atulravi/picuno/RP2040/software/circuitpython/custom-firmware-2-apr/readme.md

Contains latest Circuit Python package built for Picuno. Yet to request Pull Request. Will do so after files are confirmed to work properly.

<i>Last build date:</i><b>02-Apr-2024</b>
