atulravi/picuno/RP2040/v2/visualplace/readme.md

Files for use in visualPlace for easy assembly of latest PicUNO boards which are production ready without component markers. VisualPlace will display the location of components on the PCB with the BOM and POS files which are provided. 

Download Visual Place here: <a href="https://www.compuphase.com/visualplace/visualplace_en.htm">https://www.compuphase.com/visualplace/visualplace_en.htm</a>
