atulravi/picuno/RP2040/v2/visualplace/2.2.3/readme.md

COntains BOM, Placement file and gerbers to use in VisualPlace for easy assembly.
