atulravi/picuno/RP2040/v2/kicad/v2.2/readme.md

V2.2 with resettable fuse, level shifitng on GPIO 0-5 and standardised 0603 parts for easier assembly. Routing improved in various areas.<br>
Unnecessary vias removed. <br>
Possibly last iteration with changes suggested. <br>
Sparkfun QWIIC added. New notations added. SHall be fabricated for testing soon.
