atulravi/picuno/RP2040/v2/kicad/v2.1/readme.md

Kicad Files for 2.1 with level shifters on GPIO 0-5 and reset pin added.
