atulravi/picuno/RP2040/v2/visualplace/2.2.3/gerbers/readme.md

Gerbers for use in VisualPlace of 2.2.3 ALso applies to 3.3- 1.2.3
