atulravi/picuno/RP2040/v2/kicad/v2.2/2.2.3/readme.md

Final version of the Picuno which will be manufactured soon and is being prototyped as of upload date. KiCad files.
