atulravi/picuno/RP2040/v2/kicad/v2.2/v2.2.1/readme.md

Added India Flag under Flash. Our commitment to Made IN India. Also minor changes. <br>
Also removed 2 logic level changers since cruicial RX TX pins for BLE etc were getting blocked. Not considering replacing it for all pins. <br>
Since 3.3V inputs will be level shifted to 5V. Inputs are not allowed on GPIOs 2-6. Others are perfectly fine. <br>
Qwiic added. Logos added.
