atulravi/picuno/RP2040/v2/scheme-gerbers/gerbers/v2.2/readme.md

Gerbers of  V2.2. Differential routing errors fixed. Minor routing changes. Level Shifting ans QWIIC added.
