atulravi/picuno/RP2040/v2/scheme-gerbers/gerbers/v2.2/2.5.0/README.md

V2.5 Gerbers and files for PicUNO. IOREF issue and RESET PIN issue fixed.
