atulravi/picuno/RP2040/v2/scheme-gerbers/gerbers/v2.2/2.2.5/readme.md

Contains the updated Gerbers for the PicUNO with the IOREF issue fixed.
