atulravi/picuno/RP2040/v2/scheme-gerbers/gerbers/v2.2/v2.2.2/readme.md

V2.2.2 of the Picuno with the Level shifting on the top half of the board. This has been done for easier assembly. Possibly final variant.
