atulravi/picuno/RP2040/v2/scheme-gerbers/gerbers/v2.2/v2.2.1/readme.md

Gerbers with India flag and 2 logic level shifters removed since crucial UART pins were blocked. Also interchanged RX an TX pins to original Arduino UNO posistion upon suggestions. India Flag added due to our commitment of Mae In India!
