atulravi/picuno/RP2040/software/micropython/02-APR-24/frozen_content.c

//
// Content for MICROPY_MODULE_FROZEN_STR
//
#include <stdint.h>
#define MP_FROZEN_STR_NAMES \

const uint32_t mp_frozen_str_sizes[] = { 0 };
const char mp_frozen_str_content[] = {
"\0"
};

//
// Content for MICROPY_MODULE_FROZEN_MPY
//
#include "py/mpconfig.h"
#include "py/objint.h"
#include "py/objstr.h"
#include "py/emitglue.h"
#include "py/nativeglue.h"

#if MICROPY_LONGINT_IMPL != 2
#error "incompatible MICROPY_LONGINT_IMPL"
#endif

#if MPZ_DIG_SIZE != 16
#error "incompatible MPZ_DIG_SIZE"
#endif

#if MICROPY_PY_BUILTINS_FLOAT
typedef struct _mp_obj_float_t {
    mp_obj_base_t base;
    mp_float_t value;
} mp_obj_float_t;
#endif

#if MICROPY_PY_BUILTINS_COMPLEX
typedef struct _mp_obj_complex_t {
    mp_obj_base_t base;
    mp_float_t real;
    mp_float_t imag;
} mp_obj_complex_t;
#endif

enum {
    MP_QSTR_0_dot_1_dot_0 = MP_QSTRnumber_of,
    MP_QSTR_CRC_space_error,
    MP_QSTR_DHT11,
    MP_QSTR_DHT22,
    MP_QSTR_DHTBase,
    MP_QSTR_DS18X20,
    MP_QSTR_Event,
    MP_QSTR_H,
    MP_QSTR_IOQueue,
    MP_QSTR_Lock,
    MP_QSTR_Lock_space_not_space_acquired,
    MP_QSTR_Loop,
    MP_QSTR_MATCH_ROM,
    MP_QSTR_NeoPixel,
    MP_QSTR_ORDER,
    MP_QSTR_OneWire,
    MP_QSTR_OneWireError,
    MP_QSTR_PIOASMEmit,
    MP_QSTR_PIOASMError,
    MP_QSTR_PROTOCOL_TLS_CLIENT,
    MP_QSTR_SEARCH_ROM,
    MP_QSTR_SKIP_ROM,
    MP_QSTR_SOCK_STREAM,
    MP_QSTR_SOL_SOCKET,
    MP_QSTR_SO_REUSEADDR,
    MP_QSTR_SSLContext,
    MP_QSTR_Server,
    MP_QSTR_SingletonGenerator,
    MP_QSTR_Stream,
    MP_QSTR_StreamReader,
    MP_QSTR_StreamWriter,
    MP_QSTR_ThreadSafeFlag,
    MP_QSTR_TimeoutError,
    MP_QSTR__Remove,
    MP_QSTR___version__,
    MP_QSTR__attrs,
    MP_QSTR__boot_dot_py,
    MP_QSTR__boot_fat_dot_py,
    MP_QSTR__dequeue,
    MP_QSTR__enqueue,
    MP_QSTR__exc_context,
    MP_QSTR__exc_handler,
    MP_QSTR__io_queue,
    MP_QSTR__ow,
    MP_QSTR__pio_funcs,
    MP_QSTR__promote_to_task,
    MP_QSTR__run,
    MP_QSTR__search_rom,
    MP_QSTR__serve,
    MP_QSTR__stop_task,
    MP_QSTR__stopper,
    MP_QSTR_accept,
    MP_QSTR_aclose,
    MP_QSTR_asm_pio,
    MP_QSTR_asyncio,
    MP_QSTR_asyncio_slash___init___dot_py,
    MP_QSTR_asyncio_slash_core_dot_py,
    MP_QSTR_asyncio_slash_event_dot_py,
    MP_QSTR_asyncio_slash_funcs_dot_py,
    MP_QSTR_asyncio_slash_lock_dot_py,
    MP_QSTR_asyncio_slash_stream_dot_py,
    MP_QSTR_attr,
    MP_QSTR_autopull,
    MP_QSTR_autopush,
    MP_QSTR_aw,
    MP_QSTR_awrite,
    MP_QSTR_awritestr,
    MP_QSTR_backlog,
    MP_QSTR_bdev,
    MP_QSTR_bind,
    MP_QSTR_block,
    MP_QSTR_bpp,
    MP_QSTR_call_exception_handler,
    MP_QSTR_can_squot_t_space_gather,
    MP_QSTR_cb,
    MP_QSTR_checksum_space_error,
    MP_QSTR_cond,
    MP_QSTR_connect,
    MP_QSTR_context,
    MP_QSTR_convert_temp,
    MP_QSTR_core,
    MP_QSTR_coro_equals_,
    MP_QSTR_coroutine_space_expected,
    MP_QSTR_create_task,
    MP_QSTR_current_task,
    MP_QSTR_dec,
    MP_QSTR_default_exception_handler,
    MP_QSTR_delay,
    MP_QSTR_delay_space_too_space_large,
    MP_QSTR_delay_max,
    MP_QSTR_dest,
    MP_QSTR_dht_dot_py,
    MP_QSTR_diff,
    MP_QSTR_do_handshake_on_connect,
    MP_QSTR_drain,
    MP_QSTR_ds18x20_dot_py,
    MP_QSTR_dt,
    MP_QSTR_duplicate_space_label_space__brace_open__brace_close_,
    MP_QSTR_er,
    MP_QSTR_esp,
    MP_QSTR_event,
    MP_QSTR_exc,
    MP_QSTR_exc_type,
    MP_QSTR_exception,
    MP_QSTR_f,
    MP_QSTR_fifo_join,
    MP_QSTR_fs,
    MP_QSTR_funcs,
    MP_QSTR_future,
    MP_QSTR_future_colon_,
    MP_QSTR_gather,
    MP_QSTR_get_event_loop,
    MP_QSTR_get_exception_handler,
    MP_QSTR_get_extra_info,
    MP_QSTR_getaddrinfo,
    MP_QSTR_gpio,
    MP_QSTR_host,
    MP_QSTR_humidity,
    MP_QSTR_i,
    MP_QSTR_idx,
    MP_QSTR_ifempty,
    MP_QSTR_iffull,
    MP_QSTR_in_,
    MP_QSTR_instr,
    MP_QSTR_invalid_space_bit_space_count_space__brace_open__brace_close_,
    MP_QSTR_is_set,
    MP_QSTR_isr,
    MP_QSTR_jmp,
    MP_QSTR_l_rom,
    MP_QSTR_labels,
    MP_QSTR_listen,
    MP_QSTR_loop,
    MP_QSTR_main_task,
    MP_QSTR_measure,
    MP_QSTR_message,
    MP_QSTR_mod,
    MP_QSTR_n,
    MP_QSTR_neopixel_dot_py,
    MP_QSTR_new_event_loop,
    MP_QSTR_no_space_running_space_event_space_loop,
    MP_QSTR_no_space_sideset,
    MP_QSTR_noblock,
    MP_QSTR_not_osre,
    MP_QSTR_not_x,
    MP_QSTR_not_y,
    MP_QSTR_null,
    MP_QSTR_num_instr,
    MP_QSTR_num_sideset,
    MP_QSTR_onewire_dot_py,
    MP_QSTR_open_connection,
    MP_QSTR_osr,
    MP_QSTR_out,
    MP_QSTR_out_buf,
    MP_QSTR_out_init,
    MP_QSTR_ow,
    MP_QSTR_pass_,
    MP_QSTR_pc,
    MP_QSTR_peername,
    MP_QSTR_pin,
    MP_QSTR_pindirs,
    MP_QSTR_pins,
    MP_QSTR_poller,
    MP_QSTR_port,
    MP_QSTR_pyb,
    MP_QSTR_pyboard,
    MP_QSTR_queue_read,
    MP_QSTR_queue_write,
    MP_QSTR_read_scratch,
    MP_QSTR_read_temp,
    MP_QSTR_readexactly,
    MP_QSTR_rel,
    MP_QSTR_req,
    MP_QSTR_required,
    MP_QSTR_return_exceptions,
    MP_QSTR_rom,
    MP_QSTR_rp2_dot_py,
    MP_QSTR_run,
    MP_QSTR_run_forever,
    MP_QSTR_run_until_complete,
    MP_QSTR_runq_len,
    MP_QSTR_s,
    MP_QSTR_select_rom,
    MP_QSTR_server_hostname,
    MP_QSTR_server_side,
    MP_QSTR_set_exception_handler,
    MP_QSTR_set_init,
    MP_QSTR_setblocking,
    MP_QSTR_setsockopt,
    MP_QSTR_sgen,
    MP_QSTR_side,
    MP_QSTR_sideset_space_too_space_large,
    MP_QSTR_sideset_count,
    MP_QSTR_sideset_init,
    MP_QSTR_sideset_opt,
    MP_QSTR_socket,
    MP_QSTR_src,
    MP_QSTR_ssl,
    MP_QSTR_start_pass,
    MP_QSTR_start_server,
    MP_QSTR_status,
    MP_QSTR_stream,
    MP_QSTR_stream_awrite,
    MP_QSTR_sz,
    MP_QSTR_t,
    MP_QSTR_task,
    MP_QSTR_tb,
    MP_QSTR_temperature,
    MP_QSTR_ticks,
    MP_QSTR_timing,
    MP_QSTR_uasyncio_dot_py,
    MP_QSTR_unknown_space_label_space__brace_open__brace_close_,
    MP_QSTR_v,
    MP_QSTR_value2,
    MP_QSTR_wait,
    MP_QSTR_wait_closed,
    MP_QSTR_wait_for,
    MP_QSTR_wait_for_ms,
    MP_QSTR_wait_io_event,
    MP_QSTR_waiter,
    MP_QSTR_waiting,
    MP_QSTR_waitq_len,
    MP_QSTR_word,
    MP_QSTR_wrap,
    MP_QSTR_wrap_socket,
    MP_QSTR_wrap_target,
    MP_QSTR_wrap_used,
    MP_QSTR_write_scratch,
    MP_QSTR_x,
    MP_QSTR_x_dec,
    MP_QSTR_x_not_y,
    MP_QSTR_y,
    MP_QSTR_y_dec,
};

const qstr_hash_t mp_qstr_frozen_const_hashes[] = {
    20,
    79,
    93,
    253,
    40,
    1,
    233,
    237,
    146,
    142,
    167,
    25,
    185,
    105,
    75,
    104,
    80,
    121,
    244,
    225,
    164,
    203,
    50,
    15,
    33,
    214,
    160,
    57,
    57,
    156,
    54,
    86,
    102,
    124,
    63,
    26,
    171,
    71,
    106,
    192,
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
};

const qstr_len_t mp_qstr_frozen_const_lengths[] = {
    5,
    9,
    5,
    5,
    7,
    7,
    5,
    1,
    7,
    4,
    17,
    4,
    9,
    8,
    5,
    7,
    12,
    10,
    11,
    19,
    10,
    8,
    11,
    10,
    12,
    10,
    6,
    18,
    6,
    12,
    12,
    14,
    12,
    7,
    11,
    6,
    8,
    12,
    8,
    8,
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
};

extern const qstr_pool_t mp_qstr_const_pool;
const qstr_pool_t mp_qstr_frozen_const_pool = {
    &mp_qstr_const_pool, // previous pool
    MP_QSTRnumber_of, // previous pool size
    true, // is_sorted
    10, // allocated entries
    232, // used entries
    (qstr_hash_t *)mp_qstr_frozen_const_hashes,
    (qstr_len_t *)mp_qstr_frozen_const_lengths,
    {
        "0.1.0",
        "CRC error",
        "DHT11",
        "DHT22",
        "DHTBase",
        "DS18X20",
        "Event",
        "H",
        "IOQueue",
        "Lock",
        "Lock not acquired",
        "Loop",
        "MATCH_ROM",
        "NeoPixel",
        "ORDER",
        "OneWire",
        "OneWireError",
        "PIOASMEmit",
        "PIOASMError",
        "PROTOCOL_TLS_CLIENT",
        "SEARCH_ROM",
        "SKIP_ROM",
        "SOCK_STREAM",
        "SOL_SOCKET",
        "SO_REUSEADDR",
        "SSLContext",
        "Server",
        "SingletonGenerator",
        "Stream",
        "StreamReader",
        "StreamWriter",
        "ThreadSafeFlag",
        "TimeoutError",
        "_Remove",
        "__version__",
        "_attrs",
        "_boot.py",
        "_boot_fat.py",
        "_dequeue",
        "_enqueue",
        "_exc_context",
        "_exc_handler",
        "_io_queue",
        "_ow",
        "_pio_funcs",
        "_promote_to_task",
        "_run",
        "_search_rom",
        "_serve",
        "_stop_task",
        "_stopper",
        "accept",
        "aclose",
        "asm_pio",
        "asyncio",
        "asyncio/__init__.py",
        "asyncio/core.py",
        "asyncio/event.py",
        "asyncio/funcs.py",
        "asyncio/lock.py",
        "asyncio/stream.py",
        "attr",
        "autopull",
        "autopush",
        "aw",
        "awrite",
        "awritestr",
        "backlog",
        "bdev",
        "bind",
        "block",
        "bpp",
        "call_exception_handler",
        "can't gather",
        "cb",
        "checksum error",
        "cond",
        "connect",
        "context",
        "convert_temp",
        "core",
        "coro=",
        "coroutine expected",
        "create_task",
        "current_task",
        "dec",
        "default_exception_handler",
        "delay",
        "delay too large",
        "delay_max",
        "dest",
        "dht.py",
        "diff",
        "do_handshake_on_connect",
        "drain",
        "ds18x20.py",
        "dt",
        "duplicate label {}",
        "er",
        "esp",
        "event",
        "exc",
        "exc_type",
        "exception",
        "f",
        "fifo_join",
        "fs",
        "funcs",
        "future",
        "future:",
        "gather",
        "get_event_loop",
        "get_exception_handler",
        "get_extra_info",
        "getaddrinfo",
        "gpio",
        "host",
        "humidity",
        "i",
        "idx",
        "ifempty",
        "iffull",
        "in_",
        "instr",
        "invalid bit count {}",
        "is_set",
        "isr",
        "jmp",
        "l_rom",
        "labels",
        "listen",
        "loop",
        "main_task",
        "measure",
        "message",
        "mod",
        "n",
        "neopixel.py",
        "new_event_loop",
        "no running event loop",
        "no sideset",
        "noblock",
        "not_osre",
        "not_x",
        "not_y",
        "null",
        "num_instr",
        "num_sideset",
        "onewire.py",
        "open_connection",
        "osr",
        "out",
        "out_buf",
        "out_init",
        "ow",
        "pass_",
        "pc",
        "peername",
        "pin",
        "pindirs",
        "pins",
        "poller",
        "port",
        "pyb",
        "pyboard",
        "queue_read",
        "queue_write",
        "read_scratch",
        "read_temp",
        "readexactly",
        "rel",
        "req",
        "required",
        "return_exceptions",
        "rom",
        "rp2.py",
        "run",
        "run_forever",
        "run_until_complete",
        "runq_len",
        "s",
        "select_rom",
        "server_hostname",
        "server_side",
        "set_exception_handler",
        "set_init",
        "setblocking",
        "setsockopt",
        "sgen",
        "side",
        "sideset too large",
        "sideset_count",
        "sideset_init",
        "sideset_opt",
        "socket",
        "src",
        "ssl",
        "start_pass",
        "start_server",
        "status",
        "stream",
        "stream_awrite",
        "sz",
        "t",
        "task",
        "tb",
        "temperature",
        "ticks",
        "timing",
        "uasyncio.py",
        "unknown label {}",
        "v",
        "value2",
        "wait",
        "wait_closed",
        "wait_for",
        "wait_for_ms",
        "wait_io_event",
        "waiter",
        "waiting",
        "waitq_len",
        "word",
        "wrap",
        "wrap_socket",
        "wrap_target",
        "wrap_used",
        "write_scratch",
        "x",
        "x_dec",
        "x_not_y",
        "y",
        "y_dec",
    },
};

////////////////////////////////////////////////////////////////////////////////
// frozen module _boot_fat
// - original source file: /home/atul/micropython/ports/rp2/build-ATRIVATECH_PICUNO/frozen_mpy/_boot_fat.mpy
// - frozen file name: _boot_fat.py
// - .mpy header: 4d:06:00:1f

// frozen bytecode for file _boot_fat.py, scope _boot_fat__lt_module_gt_
static const byte fun_data__boot_fat__lt_module_gt_[96] = {
    0x2c,0x14, // prelude
    0x01, // names: <module>
    0x26,0x6c,0x20,0x28,0x22,0x4d,0x2b,0x2d,0x4b, // code info
    0x80, // LOAD_CONST_SMALL_INT 0
    0x51, // LOAD_CONST_NONE
    0x1b,0x02, // IMPORT_NAME 'vfs'
    0x16,0x02, // STORE_NAME 'vfs'
    0x80, // LOAD_CONST_SMALL_INT 0
    0x51, // LOAD_CONST_NONE
    0x1b,0x03, // IMPORT_NAME 'machine'
    0x16,0x03, // STORE_NAME 'machine'
    0x80, // LOAD_CONST_SMALL_INT 0
    0x51, // LOAD_CONST_NONE
    0x1b,0x04, // IMPORT_NAME 'rp2'
    0x16,0x04, // STORE_NAME 'rp2'
    0x11,0x04, // LOAD_NAME 'rp2'
    0x14,0x05, // LOAD_METHOD 'Flash'
    0x36,0x00, // CALL_METHOD 0
    0x16,0x0a, // STORE_NAME 'bdev'
    0x48,0x0c, // SETUP_EXCEPT 12
    0x11,0x02, // LOAD_NAME 'vfs'
    0x14,0x06, // LOAD_METHOD 'VfsFat'
    0x11,0x0a, // LOAD_NAME 'bdev'
    0x36,0x01, // CALL_METHOD 1
    0x16,0x0b, // STORE_NAME 'fs'
    0x4a,0x19, // POP_EXCEPT_JUMP 25
    0x59, // POP_TOP
    0x11,0x02, // LOAD_NAME 'vfs'
    0x13,0x06, // LOAD_ATTR 'VfsFat'
    0x14,0x07, // LOAD_METHOD 'mkfs'
    0x11,0x0a, // LOAD_NAME 'bdev'
    0x36,0x01, // CALL_METHOD 1
    0x59, // POP_TOP
    0x11,0x02, // LOAD_NAME 'vfs'
    0x14,0x06, // LOAD_METHOD 'VfsFat'
    0x11,0x0a, // LOAD_NAME 'bdev'
    0x36,0x01, // CALL_METHOD 1
    0x16,0x0b, // STORE_NAME 'fs'
    0x4a,0x01, // POP_EXCEPT_JUMP 1
    0x5d, // END_FINALLY
    0x11,0x02, // LOAD_NAME 'vfs'
    0x14,0x08, // LOAD_METHOD 'mount'
    0x11,0x0b, // LOAD_NAME 'fs'
    0x10,0x09, // LOAD_CONST_STRING '/'
    0x36,0x02, // CALL_METHOD 2
    0x59, // POP_TOP
    0x19,0x02, // DELETE_NAME 'vfs'
    0x19,0x0a, // DELETE_NAME 'bdev'
    0x19,0x0b, // DELETE_NAME 'fs'
    0x51, // LOAD_CONST_NONE
    0x63, // RETURN_VALUE
};
#if MICROPY_PERSISTENT_CODE_SAVE
static const mp_raw_code_truncated_t proto_fun__boot_fat__lt_module_gt_ = {
    .proto_fun_indicator[0] = MP_PROTO_FUN_INDICATOR_RAW_CODE_0,
    .proto_fun_indicator[1] = MP_PROTO_FUN_INDICATOR_RAW_CODE_1,
    .kind = MP_CODE_BYTECODE,
    .is_generator = 0,
    .fun_data = fun_data__boot_fat__lt_module_gt_,
    .children = NULL,
    #if MICROPY_PERSISTENT_CODE_SAVE
    .fun_data_len = 96,
    .n_children = 0,
    #if MICROPY_EMIT_MACHINE_CODE
    .prelude_offset = 0,
    #endif
    #if MICROPY_PY_SYS_SETTRACE
    .line_of_definition = 0,
    .prelude = {
        .n_state = 6,
        .n_exc_stack = 1,
        .scope_flags = 0,
        .n_pos_args = 0,
        .n_kwonly_args = 0,
        .n_def_pos_args = 0,
        .qstr_block_name_idx = 1,
        .line_info = fun_data__boot_fat__lt_module_gt_ + 3,
        .line_info_top = fun_data__boot_fat__lt_module_gt_ + 12,
        .opcodes = fun_data__boot_fat__lt_module_gt_ + 12,
    },
    #endif
    #endif
};
#else
#define proto_fun__boot_fat__lt_module_gt_ fun_data__boot_fat__lt_module_gt_[0]
#endif

static const qstr_short_t const_qstr_table_data__boot_fat[12] = {
    MP_QSTR__boot_fat_dot_py,
    MP_QSTR__lt_module_gt_,
    MP_QSTR_vfs,
    MP_QSTR_machine,
    MP_QSTR_rp2,
    MP_QSTR_Flash,
    MP_QSTR_VfsFat,
    MP_QSTR_mkfs,
    MP_QSTR_mount,
    MP_QSTR__slash_,
    MP_QSTR_bdev,
    MP_QSTR_fs,
};

static const mp_frozen_module_t frozen_module__boot_fat = {
    .constants = {
        .qstr_table = (qstr_short_t *)&const_qstr_table_data__boot_fat,
        .obj_table = NULL,
    },
    .proto_fun = &proto_fun__boot_fat__lt_module_gt_,
};

////////////////////////////////////////////////////////////////////////////////
// frozen module _boot
// - original source file: /home/atul/micropython/ports/rp2/build-ATRIVATECH_PICUNO/frozen_mpy/_boot.mpy
// - frozen file name: _boot.py
// - .mpy header: 4d:06:00:1f

// frozen bytecode for file _boot.py, scope _boot__lt_module_gt_
static const byte fun_data__boot__lt_module_gt_[114] = {
    0x3c,0x14, // prelude
    0x01, // names: <module>
    0x26,0x6c,0x40,0x28,0x22,0x53,0x31,0x33,0x4b, // code info
    0x80, // LOAD_CONST_SMALL_INT 0
    0x51, // LOAD_CONST_NONE
    0x1b,0x02, // IMPORT_NAME 'vfs'
    0x16,0x02, // STORE_NAME 'vfs'
    0x80, // LOAD_CONST_SMALL_INT 0
    0x51, // LOAD_CONST_NONE
    0x1b,0x03, // IMPORT_NAME 'machine'
    0x16,0x03, // STORE_NAME 'machine'
    0x80, // LOAD_CONST_SMALL_INT 0
    0x51, // LOAD_CONST_NONE
    0x1b,0x04, // IMPORT_NAME 'rp2'
    0x16,0x04, // STORE_NAME 'rp2'
    0x11,0x04, // LOAD_NAME 'rp2'
    0x14,0x05, // LOAD_METHOD 'Flash'
    0x36,0x00, // CALL_METHOD 0
    0x16,0x0b, // STORE_NAME 'bdev'
    0x48,0x12, // SETUP_EXCEPT 18
    0x11,0x02, // LOAD_NAME 'vfs'
    0x14,0x06, // LOAD_METHOD 'VfsLfs2'
    0x11,0x0b, // LOAD_NAME 'bdev'
    0x10,0x07, // LOAD_CONST_STRING 'progsize'
    0x22,0x82,0x00, // LOAD_CONST_SMALL_INT 256
    0x36,0x82,0x01, // CALL_METHOD 257
    0x16,0x0c, // STORE_NAME 'fs'
    0x4a,0x25, // POP_EXCEPT_JUMP 37
    0x59, // POP_TOP
    0x11,0x02, // LOAD_NAME 'vfs'
    0x13,0x06, // LOAD_ATTR 'VfsLfs2'
    0x14,0x08, // LOAD_METHOD 'mkfs'
    0x11,0x0b, // LOAD_NAME 'bdev'
    0x10,0x07, // LOAD_CONST_STRING 'progsize'
    0x22,0x82,0x00, // LOAD_CONST_SMALL_INT 256
    0x36,0x82,0x01, // CALL_METHOD 257
    0x59, // POP_TOP
    0x11,0x02, // LOAD_NAME 'vfs'
    0x14,0x06, // LOAD_METHOD 'VfsLfs2'
    0x11,0x0b, // LOAD_NAME 'bdev'
    0x10,0x07, // LOAD_CONST_STRING 'progsize'
    0x22,0x82,0x00, // LOAD_CONST_SMALL_INT 256
    0x36,0x82,0x01, // CALL_METHOD 257
    0x16,0x0c, // STORE_NAME 'fs'
    0x4a,0x01, // POP_EXCEPT_JUMP 1
    0x5d, // END_FINALLY
    0x11,0x02, // LOAD_NAME 'vfs'
    0x14,0x09, // LOAD_METHOD 'mount'
    0x11,0x0c, // LOAD_NAME 'fs'
    0x10,0x0a, // LOAD_CONST_STRING '/'
    0x36,0x02, // CALL_METHOD 2
    0x59, // POP_TOP
    0x19,0x02, // DELETE_NAME 'vfs'
    0x19,0x0b, // DELETE_NAME 'bdev'
    0x19,0x0c, // DELETE_NAME 'fs'
    0x51, // LOAD_CONST_NONE
    0x63, // RETURN_VALUE
};
#if MICROPY_PERSISTENT_CODE_SAVE
static const mp_raw_code_truncated_t proto_fun__boot__lt_module_gt_ = {
    .proto_fun_indicator[0] = MP_PROTO_FUN_INDICATOR_RAW_CODE_0,
    .proto_fun_indicator[1] = MP_PROTO_FUN_INDICATOR_RAW_CODE_1,
    .kind = MP_CODE_BYTECODE,
    .is_generator = 0,
    .fun_data = fun_data__boot__lt_module_gt_,
    .children = NULL,
    #if MICROPY_PERSISTENT_CODE_SAVE
    .fun_data_len = 114,
    .n_children = 0,
    #if MICROPY_EMIT_MACHINE_CODE
    .prelude_offset = 0,
    #endif
    #if MICROPY_PY_SYS_SETTRACE
    .line_of_definition = 0,
    .prelude = {
        .n_state = 8,
        .n_exc_stack = 1,
        .scope_flags = 0,
        .n_pos_args = 0,
        .n_kwonly_args = 0,
        .n_def_pos_args = 0,
        .qstr_block_name_idx = 1,
        .line_info = fun_data__boot__lt_module_gt_ + 3,
        .line_info_top = fun_data__boot__lt_module_gt_ + 12,
        .opcodes = fun_data__boot__lt_module_gt_ + 12,
    },
    #endif
    #endif
};
#else
#define proto_fun__boot__lt_module_gt_ fun_data__boot__lt_module_gt_[0]
#endif

static const qstr_short_t const_qstr_table_data__boot[13] = {
    MP_QSTR__boot_dot_py,
    MP_QSTR__lt_module_gt_,
    MP_QSTR_vfs,
    MP_QSTR_machine,
    MP_QSTR_rp2,
    MP_QSTR_Flash,
    MP_QSTR_VfsLfs2,
    MP_QSTR_progsize,
    MP_QSTR_mkfs,
    MP_QSTR_mount,
    MP_QSTR__slash_,
    MP_QSTR_bdev,
    MP_QSTR_fs,
};

static const mp_frozen_module_t frozen_module__boot = {
    .constants = {
        .qstr_table = (qstr_short_t *)&const_qstr_table_data__boot,
        .obj_table = NULL,
    },
    .proto_fun = &proto_fun__boot__lt_module_gt_,
};

////////////////////////////////////////////////////////////////////////////////
// frozen module rp2
// - original source file: /home/atul/micropython/ports/rp2/build-ATRIVATECH_PICUNO/frozen_mpy/rp2.mpy
// - frozen file name: rp2.py
// - .mpy header: 4d:06:00:1f

// frozen bytecode for file rp2.py, scope rp2__lt_module_gt_
static const byte fun_data_rp2__lt_module_gt_[284] = {
    0x18,0x6e, // prelude
    0x01, // names: <module>
    0x60,0x28,0x8c,0x0d,0x6b,0x20,0x89,0x9e,0x42,0x64,0x20,0x24,0x24,0x24,0x24,0x24,0x24,0x24,0x24,0x24,0x44,0x25,0x45,0x24,0x24,0x24,0x24,0x24,0x24,0x44,0x24,0x24,0x26,0x66,0x20,0x26,0x45,0x24,0x24,0x24,0x24,0x24,0x24,0x24,0x24,0x24,0x24,0x24,0x24,0x24,0x66,0x20,0x84,0x29, // code info
    0x80, // LOAD_CONST_SMALL_INT 0
    0x10,0x02, // LOAD_CONST_STRING '*'
    0x2a,0x01, // BUILD_TUPLE 1
    0x1b,0x03, // IMPORT_NAME '_rp2'
    0x69, // IMPORT_STAR
    0x80, // LOAD_CONST_SMALL_INT 0
    0x10,0x04, // LOAD_CONST_STRING 'const'
    0x2a,0x01, // BUILD_TUPLE 1
    0x1b,0x05, // IMPORT_NAME 'micropython'
    0x1c,0x04, // IMPORT_FROM 'const'
    0x16,0x04, // STORE_NAME 'const'
    0x59, // POP_TOP
    0x54, // LOAD_BUILD_CLASS
    0x32,0x00, // MAKE_FUNCTION 0
    0x10,0x06, // LOAD_CONST_STRING 'PIOASMError'
    0x11,0x55, // LOAD_NAME 'Exception'
    0x34,0x03, // CALL_FUNCTION 3
    0x16,0x06, // STORE_NAME 'PIOASMError'
    0x54, // LOAD_BUILD_CLASS
    0x32,0x01, // MAKE_FUNCTION 1
    0x10,0x07, // LOAD_CONST_STRING 'PIOASMEmit'
    0x34,0x02, // CALL_FUNCTION 2
    0x16,0x07, // STORE_NAME 'PIOASMEmit'
    0x2c,0x28, // BUILD_MAP 40
    0x80, // LOAD_CONST_SMALL_INT 0
    0x10,0x08, // LOAD_CONST_STRING 'gpio'
    0x62, // STORE_MAP
    0x80, // LOAD_CONST_SMALL_INT 0
    0x10,0x09, // LOAD_CONST_STRING 'pins'
    0x62, // STORE_MAP
    0x81, // LOAD_CONST_SMALL_INT 1
    0x10,0x0a, // LOAD_CONST_STRING 'x'
    0x62, // STORE_MAP
    0x82, // LOAD_CONST_SMALL_INT 2
    0x10,0x0b, // LOAD_CONST_STRING 'y'
    0x62, // STORE_MAP
    0x83, // LOAD_CONST_SMALL_INT 3
    0x10,0x0c, // LOAD_CONST_STRING 'null'
    0x62, // STORE_MAP
    0x84, // LOAD_CONST_SMALL_INT 4
    0x10,0x0d, // LOAD_CONST_STRING 'pindirs'
    0x62, // STORE_MAP
    0x85, // LOAD_CONST_SMALL_INT 5
    0x10,0x0e, // LOAD_CONST_STRING 'pc'
    0x62, // STORE_MAP
    0x85, // LOAD_CONST_SMALL_INT 5
    0x10,0x0f, // LOAD_CONST_STRING 'status'
    0x62, // STORE_MAP
    0x86, // LOAD_CONST_SMALL_INT 6
    0x10,0x10, // LOAD_CONST_STRING 'isr'
    0x62, // STORE_MAP
    0x87, // LOAD_CONST_SMALL_INT 7
    0x10,0x11, // LOAD_CONST_STRING 'osr'
    0x62, // STORE_MAP
    0x88, // LOAD_CONST_SMALL_INT 8
    0x10,0x12, // LOAD_CONST_STRING 'exec'
    0x62, // STORE_MAP
    0x32,0x02, // MAKE_FUNCTION 2
    0x10,0x13, // LOAD_CONST_STRING 'invert'
    0x62, // STORE_MAP
    0x32,0x03, // MAKE_FUNCTION 3
    0x10,0x14, // LOAD_CONST_STRING 'reverse'
    0x62, // STORE_MAP
    0x81, // LOAD_CONST_SMALL_INT 1
    0x10,0x15, // LOAD_CONST_STRING 'not_x'
    0x62, // STORE_MAP
    0x82, // LOAD_CONST_SMALL_INT 2
    0x10,0x16, // LOAD_CONST_STRING 'x_dec'
    0x62, // STORE_MAP
    0x83, // LOAD_CONST_SMALL_INT 3
    0x10,0x17, // LOAD_CONST_STRING 'not_y'
    0x62, // STORE_MAP
    0x84, // LOAD_CONST_SMALL_INT 4
    0x10,0x18, // LOAD_CONST_STRING 'y_dec'
    0x62, // STORE_MAP
    0x85, // LOAD_CONST_SMALL_INT 5
    0x10,0x19, // LOAD_CONST_STRING 'x_not_y'
    0x62, // STORE_MAP
    0x86, // LOAD_CONST_SMALL_INT 6
    0x10,0x1a, // LOAD_CONST_STRING 'pin'
    0x62, // STORE_MAP
    0x87, // LOAD_CONST_SMALL_INT 7
    0x10,0x1b, // LOAD_CONST_STRING 'not_osre'
    0x62, // STORE_MAP
    0x81, // LOAD_CONST_SMALL_INT 1
    0x10,0x1c, // LOAD_CONST_STRING 'noblock'
    0x62, // STORE_MAP
    0xa1, // LOAD_CONST_SMALL_INT 33
    0x10,0x1d, // LOAD_CONST_STRING 'block'
    0x62, // STORE_MAP
    0x22,0x80,0x40, // LOAD_CONST_SMALL_INT 64
    0x10,0x1e, // LOAD_CONST_STRING 'iffull'
    0x62, // STORE_MAP
    0x22,0x80,0x40, // LOAD_CONST_SMALL_INT 64
    0x10,0x1f, // LOAD_CONST_STRING 'ifempty'
    0x62, // STORE_MAP
    0x22,0x80,0x40, // LOAD_CONST_SMALL_INT 64
    0x10,0x20, // LOAD_CONST_STRING 'clear'
    0x62, // STORE_MAP
    0x32,0x04, // MAKE_FUNCTION 4
    0x10,0x21, // LOAD_CONST_STRING 'rel'
    0x62, // STORE_MAP
    0x51, // LOAD_CONST_NONE
    0x10,0x22, // LOAD_CONST_STRING 'wrap_target'
    0x62, // STORE_MAP
    0x51, // LOAD_CONST_NONE
    0x10,0x23, // LOAD_CONST_STRING 'wrap'
    0x62, // STORE_MAP
    0x51, // LOAD_CONST_NONE
    0x10,0x24, // LOAD_CONST_STRING 'label'
    0x62, // STORE_MAP
    0x51, // LOAD_CONST_NONE
    0x10,0x25, // LOAD_CONST_STRING 'word'
    0x62, // STORE_MAP
    0x51, // LOAD_CONST_NONE
    0x10,0x26, // LOAD_CONST_STRING 'nop'
    0x62, // STORE_MAP
    0x51, // LOAD_CONST_NONE
    0x10,0x27, // LOAD_CONST_STRING 'jmp'
    0x62, // STORE_MAP
    0x51, // LOAD_CONST_NONE
    0x10,0x28, // LOAD_CONST_STRING 'wait'
    0x62, // STORE_MAP
    0x51, // LOAD_CONST_NONE
    0x10,0x29, // LOAD_CONST_STRING 'in_'
    0x62, // STORE_MAP
    0x51, // LOAD_CONST_NONE
    0x10,0x2a, // LOAD_CONST_STRING 'out'
    0x62, // STORE_MAP
    0x51, // LOAD_CONST_NONE
    0x10,0x2b, // LOAD_CONST_STRING 'push'
    0x62, // STORE_MAP
    0x51, // LOAD_CONST_NONE
    0x10,0x2c, // LOAD_CONST_STRING 'pull'
    0x62, // STORE_MAP
    0x51, // LOAD_CONST_NONE
    0x10,0x2d, // LOAD_CONST_STRING 'mov'
    0x62, // STORE_MAP
    0x51, // LOAD_CONST_NONE
    0x10,0x2e, // LOAD_CONST_STRING 'irq'
    0x62, // STORE_MAP
    0x51, // LOAD_CONST_NONE
    0x10,0x2f, // LOAD_CONST_STRING 'set'
    0x62, // STORE_MAP
    0x16,0x56, // STORE_NAME '_pio_funcs'
    0x32,0x05, // MAKE_FUNCTION 5
    0x16,0x3b, // STORE_NAME 'asm_pio'
    0x50, // LOAD_CONST_FALSE
    0x2a,0x01, // BUILD_TUPLE 1
    0x53, // LOAD_NULL
    0x33,0x06, // MAKE_FUNCTION_DEFARGS 6
    0x16,0x3c, // STORE_NAME 'asm_pio_encode'
    0x51, // LOAD_CONST_NONE
    0x63, // RETURN_VALUE
};
// child of rp2__lt_module_gt_
// frozen bytecode for file rp2.py, scope rp2_PIOASMError
static const byte fun_data_rp2_PIOASMError[15] = {
    0x00,0x06, // prelude
    0x06, // names: PIOASMError
    0x88,0x12, // code info
    0x11,0x57, // LOAD_NAME '__name__'
    0x16,0x58, // STORE_NAME '__module__'
    0x10,0x06, // LOAD_CONST_STRING 'PIOASMError'
    0x16,0x59, // STORE_NAME '__qualname__'
    0x51, // LOAD_CONST_NONE
    0x63, // RETURN_VALUE
};
#if MICROPY_PERSISTENT_CODE_SAVE
static const mp_raw_code_truncated_t proto_fun_rp2_PIOASMError = {
    .proto_fun_indicator[0] = MP_PROTO_FUN_INDICATOR_RAW_CODE_0,
    .proto_fun_indicator[1] = MP_PROTO_FUN_INDICATOR_RAW_CODE_1,
    .kind = MP_CODE_BYTECODE,
    .is_generator = 0,
    .fun_data = fun_data_rp2_PIOASMError,
    .children = NULL,
    #if MICROPY_PERSISTENT_CODE_SAVE
    .fun_data_len = 15,
    .n_children = 0,
    #if MICROPY_EMIT_MACHINE_CODE
    .prelude_offset = 0,
    #endif
    #if MICROPY_PY_SYS_SETTRACE
    .line_of_definition = 0,
    .prelude = {
        .n_state = 1,
        .n_exc_stack = 0,
        .scope_flags = 0,
        .n_pos_args = 0,
        .n_kwonly_args = 0,
        .n_def_pos_args = 0,
        .qstr_block_name_idx = 6,
        .line_info = fun_data_rp2_PIOASMError + 3,
        .line_info_top = fun_data_rp2_PIOASMError + 5,
        .opcodes = fun_data_rp2_PIOASMError + 5,
    },
    #endif
    #endif
};
#else
#define proto_fun_rp2_PIOASMError fun_data_rp2_PIOASMError[0]
#endif

// child of rp2__lt_module_gt_
// frozen bytecode for file rp2.py, scope rp2_PIOASMEmit
static const byte fun_data_rp2_PIOASMEmit[191] = {
    0x18,0x4c, // prelude
    0x07, // names: PIOASMEmit
    0x88,0x16,0x1f,0x70,0x80,0x25,0x84,0x0f,0x64,0x84,0x07,0x84,0x0b,0x64,0x64,0x40,0x64,0x60,0x88,0x0c,0x64,0x68,0x60,0x84,0x07,0x64,0x40,0x84,0x07,0x69,0x60,0x69,0x60,0x64,0x40,0x68,0x60, // code info
    0x11,0x57, // LOAD_NAME '__name__'
    0x16,0x58, // STORE_NAME '__module__'
    0x10,0x07, // LOAD_CONST_STRING 'PIOASMEmit'
    0x16,0x59, // STORE_NAME '__qualname__'
    0x53, // LOAD_NULL
    0x2c,0x00, // BUILD_MAP 0
    0x51, // LOAD_CONST_NONE
    0x10,0x30, // LOAD_CONST_STRING 'out_init'
    0x62, // STORE_MAP
    0x51, // LOAD_CONST_NONE
    0x10,0x31, // LOAD_CONST_STRING 'set_init'
    0x62, // STORE_MAP
    0x51, // LOAD_CONST_NONE
    0x10,0x32, // LOAD_CONST_STRING 'sideset_init'
    0x62, // STORE_MAP
    0x80, // LOAD_CONST_SMALL_INT 0
    0x10,0x33, // LOAD_CONST_STRING 'in_shiftdir'
    0x62, // STORE_MAP
    0x80, // LOAD_CONST_SMALL_INT 0
    0x10,0x34, // LOAD_CONST_STRING 'out_shiftdir'
    0x62, // STORE_MAP
    0x50, // LOAD_CONST_FALSE
    0x10,0x35, // LOAD_CONST_STRING 'autopush'
    0x62, // STORE_MAP
    0x50, // LOAD_CONST_FALSE
    0x10,0x36, // LOAD_CONST_STRING 'autopull'
    0x62, // STORE_MAP
    0xa0, // LOAD_CONST_SMALL_INT 32
    0x10,0x37, // LOAD_CONST_STRING 'push_thresh'
    0x62, // STORE_MAP
    0xa0, // LOAD_CONST_SMALL_INT 32
    0x10,0x38, // LOAD_CONST_STRING 'pull_thresh'
    0x62, // STORE_MAP
    0x80, // LOAD_CONST_SMALL_INT 0
    0x10,0x39, // LOAD_CONST_STRING 'fifo_join'
    0x62, // STORE_MAP
    0x33,0x00, // MAKE_FUNCTION_DEFARGS 0
    0x16,0x44, // STORE_NAME '__init__'
    0x32,0x01, // MAKE_FUNCTION 1
    0x16,0x49, // STORE_NAME 'start_pass'
    0x32,0x02, // MAKE_FUNCTION 2
    0x16,0x4a, // STORE_NAME '__getitem__'
    0x32,0x03, // MAKE_FUNCTION 3
    0x16,0x4b, // STORE_NAME 'delay'
    0x32,0x04, // MAKE_FUNCTION 4
    0x16,0x4c, // STORE_NAME 'side'
    0x32,0x05, // MAKE_FUNCTION 5
    0x16,0x22, // STORE_NAME 'wrap_target'
    0x32,0x06, // MAKE_FUNCTION 6
    0x16,0x23, // STORE_NAME 'wrap'
    0x32,0x07, // MAKE_FUNCTION 7
    0x16,0x24, // STORE_NAME 'label'
    0x51, // LOAD_CONST_NONE
    0x2a,0x01, // BUILD_TUPLE 1
    0x53, // LOAD_NULL
    0x33,0x08, // MAKE_FUNCTION_DEFARGS 8
    0x16,0x25, // STORE_NAME 'word'
    0x32,0x09, // MAKE_FUNCTION 9
    0x16,0x26, // STORE_NAME 'nop'
    0x51, // LOAD_CONST_NONE
    0x2a,0x01, // BUILD_TUPLE 1
    0x53, // LOAD_NULL
    0x33,0x0a, // MAKE_FUNCTION_DEFARGS 10
    0x16,0x27, // STORE_NAME 'jmp'
    0x32,0x0b, // MAKE_FUNCTION 11
    0x16,0x28, // STORE_NAME 'wait'
    0x32,0x0c, // MAKE_FUNCTION 12
    0x16,0x29, // STORE_NAME 'in_'
    0x32,0x0d, // MAKE_FUNCTION 13
    0x16,0x2a, // STORE_NAME 'out'
    0x80, // LOAD_CONST_SMALL_INT 0
    0x80, // LOAD_CONST_SMALL_INT 0
    0x2a,0x02, // BUILD_TUPLE 2
    0x53, // LOAD_NULL
    0x33,0x0e, // MAKE_FUNCTION_DEFARGS 14
    0x16,0x2b, // STORE_NAME 'push'
    0x80, // LOAD_CONST_SMALL_INT 0
    0x80, // LOAD_CONST_SMALL_INT 0
    0x2a,0x02, // BUILD_TUPLE 2
    0x53, // LOAD_NULL
    0x33,0x0f, // MAKE_FUNCTION_DEFARGS 15
    0x16,0x2c, // STORE_NAME 'pull'
    0x32,0x10, // MAKE_FUNCTION 16
    0x16,0x2d, // STORE_NAME 'mov'
    0x51, // LOAD_CONST_NONE
    0x2a,0x01, // BUILD_TUPLE 1
    0x53, // LOAD_NULL
    0x33,0x11, // MAKE_FUNCTION_DEFARGS 17
    0x16,0x2e, // STORE_NAME 'irq'
    0x32,0x12, // MAKE_FUNCTION 18
    0x16,0x2f, // STORE_NAME 'set'
    0x51, // LOAD_CONST_NONE
    0x63, // RETURN_VALUE
};
// child of rp2_PIOASMEmit
// frozen bytecode for file rp2.py, scope rp2_PIOASMEmit___init__
static const byte fun_data_rp2_PIOASMEmit___init__[144] = {
    0xa9,0x90,0x88,0x80,0x48,0x3e, // prelude
    0x44,0x5c,0x30,0x31,0x32,0x33,0x34,0x35,0x36,0x37,0x38,0x39, // names: __init__, self, out_init, set_init, sideset_init, in_shiftdir, out_shiftdir, autopush, autopull, push_thresh, pull_thresh, fifo_join
    0x80,0x26,0x4b,0x25,0x22,0x20,0x23,0x26,0x26,0x24,0x24,0x24,0x45,0x51,0x44,0x25,0x26,0x29,0x46, // code info
    0x80, // LOAD_CONST_SMALL_INT 0
    0x10,0x45, // LOAD_CONST_STRING 'array'
    0x2a,0x01, // BUILD_TUPLE 1
    0x1b,0x45, // IMPORT_NAME 'array'
    0x1c,0x45, // IMPORT_FROM 'array'
    0xcb, // STORE_FAST 11
    0x59, // POP_TOP
    0x2c,0x00, // BUILD_MAP 0
    0xb0, // LOAD_FAST 0
    0x18,0x46, // STORE_ATTR 'labels'
    0x80, // LOAD_CONST_SMALL_INT 0
    0xcc, // STORE_FAST 12
    0xba, // LOAD_FAST 10
    0x9e, // LOAD_CONST_SMALL_INT 30
    0xf0, // BINARY_OP 25 __lshift__
    0xb9, // LOAD_FAST 9
    0x9f, // LOAD_CONST_SMALL_INT 31
    0xef, // BINARY_OP 24 __and__
    0x99, // LOAD_CONST_SMALL_INT 25
    0xf0, // BINARY_OP 25 __lshift__
    0xed, // BINARY_OP 22 __or__
    0xb8, // LOAD_FAST 8
    0x9f, // LOAD_CONST_SMALL_INT 31
    0xef, // BINARY_OP 24 __and__
    0x94, // LOAD_CONST_SMALL_INT 20
    0xf0, // BINARY_OP 25 __lshift__
    0xed, // BINARY_OP 22 __or__
    0xb5, // LOAD_FAST 5
    0x93, // LOAD_CONST_SMALL_INT 19
    0xf0, // BINARY_OP 25 __lshift__
    0xed, // BINARY_OP 22 __or__
    0xb4, // LOAD_FAST 4
    0x92, // LOAD_CONST_SMALL_INT 18
    0xf0, // BINARY_OP 25 __lshift__
    0xed, // BINARY_OP 22 __or__
    0xb7, // LOAD_FAST 7
    0x91, // LOAD_CONST_SMALL_INT 17
    0xf0, // BINARY_OP 25 __lshift__
    0xed, // BINARY_OP 22 __or__
    0xb6, // LOAD_FAST 6
    0x90, // LOAD_CONST_SMALL_INT 16
    0xf0, // BINARY_OP 25 __lshift__
    0xed, // BINARY_OP 22 __or__
    0xcd, // STORE_FAST 13
    0xbb, // LOAD_FAST 11
    0x10,0x47, // LOAD_CONST_STRING 'H'
    0x34,0x01, // CALL_FUNCTION 1
    0x7f, // LOAD_CONST_SMALL_INT -1
    0x7f, // LOAD_CONST_SMALL_INT -1
    0xbc, // LOAD_FAST 12
    0xbd, // LOAD_FAST 13
    0xb1, // LOAD_FAST 1
    0xb2, // LOAD_FAST 2
    0xb3, // LOAD_FAST 3
    0x2b,0x08, // BUILD_LIST 8
    0xb0, // LOAD_FAST 0
    0x18,0x43, // STORE_ATTR 'prog'
    0x50, // LOAD_CONST_FALSE
    0xb0, // LOAD_FAST 0
    0x18,0x48, // STORE_ATTR 'wrap_used'
    0xb3, // LOAD_FAST 3
    0x51, // LOAD_CONST_NONE
    0xde, // BINARY_OP 7 <is>
    0x44,0x46, // POP_JUMP_IF_FALSE 6
    0x80, // LOAD_CONST_SMALL_INT 0
    0xb0, // LOAD_FAST 0
    0x18,0x3d, // STORE_ATTR 'sideset_count'
    0x42,0x57, // JUMP 23
    0x12,0x5d, // LOAD_GLOBAL 'isinstance'
    0xb3, // LOAD_FAST 3
    0x12,0x5e, // LOAD_GLOBAL 'int'
    0x34,0x02, // CALL_FUNCTION 2
    0x44,0x46, // POP_JUMP_IF_FALSE 6
    0x81, // LOAD_CONST_SMALL_INT 1
    0xb0, // LOAD_FAST 0
    0x18,0x3d, // STORE_ATTR 'sideset_count'
    0x42,0x48, // JUMP 8
    0x12,0x5b, // LOAD_GLOBAL 'len'
    0xb3, // LOAD_FAST 3
    0x34,0x01, // CALL_FUNCTION 1
    0xb0, // LOAD_FAST 0
    0x18,0x3d, // STORE_ATTR 'sideset_count'
    0x51, // LOAD_CONST_NONE
    0x63, // RETURN_VALUE
};
#if MICROPY_PERSISTENT_CODE_SAVE
static const mp_raw_code_truncated_t proto_fun_rp2_PIOASMEmit___init__ = {
    .proto_fun_indicator[0] = MP_PROTO_FUN_INDICATOR_RAW_CODE_0,
    .proto_fun_indicator[1] = MP_PROTO_FUN_INDICATOR_RAW_CODE_1,
    .kind = MP_CODE_BYTECODE,
    .is_generator = 0,
    .fun_data = fun_data_rp2_PIOASMEmit___init__,
    .children = NULL,
    #if MICROPY_PERSISTENT_CODE_SAVE
    .fun_data_len = 144,
    .n_children = 0,
    #if MICROPY_EMIT_MACHINE_CODE
    .prelude_offset = 0,
    #endif
    #if MICROPY_PY_SYS_SETTRACE
    .line_of_definition = 0,
    .prelude = {
        .n_state = 22,
        .n_exc_stack = 0,
        .scope_flags = 8,
        .n_pos_args = 1,
        .n_kwonly_args = 10,
        .n_def_pos_args = 0,
        .qstr_block_name_idx = 68,
        .line_info = fun_data_rp2_PIOASMEmit___init__ + 18,
        .line_info_top = fun_data_rp2_PIOASMEmit___init__ + 37,
        .opcodes = fun_data_rp2_PIOASMEmit___init__ + 37,
    },
    #endif
    #endif
};
#else
#define proto_fun_rp2_PIOASMEmit___init__ fun_data_rp2_PIOASMEmit___init__[0]
#endif

// child of rp2_PIOASMEmit
// frozen bytecode for file rp2.py, scope rp2_PIOASMEmit_start_pass
static const byte fun_data_rp2_PIOASMEmit_start_pass[110] = {
    0x2a,0x22, // prelude
    0x49,0x5c,0x40, // names: start_pass, self, pass_
    0x80,0x3f,0x26,0x2a,0x26,0x24,0x25,0x2a,0x25,0x2b,0x29,0x2b,0x24,0x24, // code info
    0xb1, // LOAD_FAST 1
    0x81, // LOAD_CONST_SMALL_INT 1
    0xd9, // BINARY_OP 2 __eq__
    0x44,0xc7,0x80, // POP_JUMP_IF_FALSE 71
    0xb0, // LOAD_FAST 0
    0x13,0x48, // LOAD_ATTR 'wrap_used'
    0x43,0x4b, // POP_JUMP_IF_TRUE 11
    0xb0, // LOAD_FAST 0
    0x13,0x41, // LOAD_ATTR 'num_instr'
    0x44,0x46, // POP_JUMP_IF_FALSE 6
    0xb0, // LOAD_FAST 0
    0x14,0x23, // LOAD_METHOD 'wrap'
    0x36,0x00, // CALL_METHOD 0
    0x59, // POP_TOP
    0x9f, // LOAD_CONST_SMALL_INT 31
    0xb0, // LOAD_FAST 0
    0x18,0x3f, // STORE_ATTR 'delay_max'
    0xb0, // LOAD_FAST 0
    0x13,0x3d, // LOAD_ATTR 'sideset_count'
    0x44,0x6e, // POP_JUMP_IF_FALSE 46
    0xb0, // LOAD_FAST 0
    0x13,0x42, // LOAD_ATTR 'num_sideset'
    0xb0, // LOAD_FAST 0
    0x13,0x41, // LOAD_ATTR 'num_instr'
    0xdc, // BINARY_OP 5 __ne__
    0xb0, // LOAD_FAST 0
    0x18,0x3e, // STORE_ATTR 'sideset_opt'
    0xb0, // LOAD_FAST 0
    0x13,0x3e, // LOAD_ATTR 'sideset_opt'
    0x44,0x54, // POP_JUMP_IF_FALSE 20
    0xb0, // LOAD_FAST 0
    0x13,0x43, // LOAD_ATTR 'prog'
    0x83, // LOAD_CONST_SMALL_INT 3
    0x58, // DUP_TOP_TWO
    0x55, // LOAD_SUBSCR
    0x23,0x01, // LOAD_CONST_OBJ 1
    0xe0, // BINARY_OP 9 __ior__
    0x5b, // ROT_THREE
    0x56, // STORE_SUBSCR
    0xb0, // LOAD_FAST 0
    0x57, // DUP_TOP
    0x13,0x3d, // LOAD_ATTR 'sideset_count'
    0x81, // LOAD_CONST_SMALL_INT 1
    0xe5, // BINARY_OP 14 __iadd__
    0x5a, // ROT_TWO
    0x18,0x3d, // STORE_ATTR 'sideset_count'
    0xb0, // LOAD_FAST 0
    0x57, // DUP_TOP
    0x13,0x3f, // LOAD_ATTR 'delay_max'
    0xb0, // LOAD_FAST 0
    0x13,0x3d, // LOAD_ATTR 'sideset_count'
    0xe4, // BINARY_OP 13 __irshift__
    0x5a, // ROT_TWO
    0x18,0x3f, // STORE_ATTR 'delay_max'
    0xb1, // LOAD_FAST 1
    0xb0, // LOAD_FAST 0
    0x18,0x40, // STORE_ATTR 'pass_'
    0x80, // LOAD_CONST_SMALL_INT 0
    0xb0, // LOAD_FAST 0
    0x18,0x41, // STORE_ATTR 'num_instr'
    0x80, // LOAD_CONST_SMALL_INT 0
    0xb0, // LOAD_FAST 0
    0x18,0x42, // STORE_ATTR 'num_sideset'
    0x51, // LOAD_CONST_NONE
    0x63, // RETURN_VALUE
};
#if MICROPY_PERSISTENT_CODE_SAVE
static const mp_raw_code_truncated_t proto_fun_rp2_PIOASMEmit_start_pass = {
    .proto_fun_indicator[0] = MP_PROTO_FUN_INDICATOR_RAW_CODE_0,
    .proto_fun_indicator[1] = MP_PROTO_FUN_INDICATOR_RAW_CODE_1,
    .kind = MP_CODE_BYTECODE,
    .is_generator = 0,
    .fun_data = fun_data_rp2_PIOASMEmit_start_pass,
    .children = NULL,
    #if MICROPY_PERSISTENT_CODE_SAVE
    .fun_data_len = 110,
    .n_children = 0,
    #if MICROPY_EMIT_MACHINE_CODE
    .prelude_offset = 0,
    #endif
    #if MICROPY_PY_SYS_SETTRACE
    .line_of_definition = 0,
    .prelude = {
        .n_state = 6,
        .n_exc_stack = 0,
        .scope_flags = 0,
        .n_pos_args = 2,
        .n_kwonly_args = 0,
        .n_def_pos_args = 0,
        .qstr_block_name_idx = 73,
        .line_info = fun_data_rp2_PIOASMEmit_start_pass + 5,
        .line_info_top = fun_data_rp2_PIOASMEmit_start_pass + 19,
        .opcodes = fun_data_rp2_PIOASMEmit_start_pass + 19,
    },
    #endif
    #endif
};
#else
#define proto_fun_rp2_PIOASMEmit_start_pass fun_data_rp2_PIOASMEmit_start_pass[0]
#endif

// child of rp2_PIOASMEmit
// frozen bytecode for file rp2.py, scope rp2_PIOASMEmit___getitem__
static const byte fun_data_rp2_PIOASMEmit___getitem__[14] = {
    0x22,0x0a, // prelude
    0x4a,0x5c,0x5f, // names: __getitem__, self, key
    0x80,0x4e, // code info
    0xb0, // LOAD_FAST 0
    0x14,0x4b, // LOAD_METHOD 'delay'
    0xb1, // LOAD_FAST 1
    0x36,0x01, // CALL_METHOD 1
    0x63, // RETURN_VALUE
};
#if MICROPY_PERSISTENT_CODE_SAVE
static const mp_raw_code_truncated_t proto_fun_rp2_PIOASMEmit___getitem__ = {
    .proto_fun_indicator[0] = MP_PROTO_FUN_INDICATOR_RAW_CODE_0,
    .proto_fun_indicator[1] = MP_PROTO_FUN_INDICATOR_RAW_CODE_1,
    .kind = MP_CODE_BYTECODE,
    .is_generator = 0,
    .fun_data = fun_data_rp2_PIOASMEmit___getitem__,
    .children = NULL,
    #if MICROPY_PERSISTENT_CODE_SAVE
    .fun_data_len = 14,
    .n_children = 0,
    #if MICROPY_EMIT_MACHINE_CODE
    .prelude_offset = 0,
    #endif
    #if MICROPY_PY_SYS_SETTRACE
    .line_of_definition = 0,
    .prelude = {
        .n_state = 5,
        .n_exc_stack = 0,
        .scope_flags = 0,
        .n_pos_args = 2,
        .n_kwonly_args = 0,
        .n_def_pos_args = 0,
        .qstr_block_name_idx = 74,
        .line_info = fun_data_rp2_PIOASMEmit___getitem__ + 5,
        .line_info_top = fun_data_rp2_PIOASMEmit___getitem__ + 7,
        .opcodes = fun_data_rp2_PIOASMEmit___getitem__ + 7,
    },
    #endif
    #endif
};
#else
#define proto_fun_rp2_PIOASMEmit___getitem__ fun_data_rp2_PIOASMEmit___getitem__[0]
#endif

// child of rp2_PIOASMEmit
// frozen bytecode for file rp2.py, scope rp2_PIOASMEmit_delay
static const byte fun_data_rp2_PIOASMEmit_delay[48] = {
    0x32,0x12, // prelude
    0x4b,0x5c,0x4b, // names: delay, self, delay
    0x80,0x51,0x27,0x27,0x27,0x2e, // code info
    0xb0, // LOAD_FAST 0
    0x13,0x40, // LOAD_ATTR 'pass_'
    0x80, // LOAD_CONST_SMALL_INT 0
    0xd8, // BINARY_OP 1 __gt__
    0x44,0x5c, // POP_JUMP_IF_FALSE 28
    0xb1, // LOAD_FAST 1
    0xb0, // LOAD_FAST 0
    0x13,0x3f, // LOAD_ATTR 'delay_max'
    0xd8, // BINARY_OP 1 __gt__
    0x44,0x47, // POP_JUMP_IF_FALSE 7
    0x12,0x06, // LOAD_GLOBAL 'PIOASMError'
    0x23,0x02, // LOAD_CONST_OBJ 2
    0x34,0x01, // CALL_FUNCTION 1
    0x65, // RAISE_OBJ
    0xb0, // LOAD_FAST 0
    0x13,0x43, // LOAD_ATTR 'prog'
    0x80, // LOAD_CONST_SMALL_INT 0
    0x55, // LOAD_SUBSCR
    0x7f, // LOAD_CONST_SMALL_INT -1
    0x58, // DUP_TOP_TWO
    0x55, // LOAD_SUBSCR
    0xb1, // LOAD_FAST 1
    0x88, // LOAD_CONST_SMALL_INT 8
    0xf0, // BINARY_OP 25 __lshift__
    0xe0, // BINARY_OP 9 __ior__
    0x5b, // ROT_THREE
    0x56, // STORE_SUBSCR
    0xb0, // LOAD_FAST 0
    0x63, // RETURN_VALUE
};
#if MICROPY_PERSISTENT_CODE_SAVE
static const mp_raw_code_truncated_t proto_fun_rp2_PIOASMEmit_delay = {
    .proto_fun_indicator[0] = MP_PROTO_FUN_INDICATOR_RAW_CODE_0,
    .proto_fun_indicator[1] = MP_PROTO_FUN_INDICATOR_RAW_CODE_1,
    .kind = MP_CODE_BYTECODE,
    .is_generator = 0,
    .fun_data = fun_data_rp2_PIOASMEmit_delay,
    .children = NULL,
    #if MICROPY_PERSISTENT_CODE_SAVE
    .fun_data_len = 48,
    .n_children = 0,
    #if MICROPY_EMIT_MACHINE_CODE
    .prelude_offset = 0,
    #endif
    #if MICROPY_PY_SYS_SETTRACE
    .line_of_definition = 0,
    .prelude = {
        .n_state = 7,
        .n_exc_stack = 0,
        .scope_flags = 0,
        .n_pos_args = 2,
        .n_kwonly_args = 0,
        .n_def_pos_args = 0,
        .qstr_block_name_idx = 75,
        .line_info = fun_data_rp2_PIOASMEmit_delay + 5,
        .line_info_top = fun_data_rp2_PIOASMEmit_delay + 11,
        .opcodes = fun_data_rp2_PIOASMEmit_delay + 11,
    },
    #endif
    #endif
};
#else
#define proto_fun_rp2_PIOASMEmit_delay fun_data_rp2_PIOASMEmit_delay[0]
#endif

// child of rp2_PIOASMEmit
// frozen bytecode for file rp2.py, scope rp2_PIOASMEmit_side
static const byte fun_data_rp2_PIOASMEmit_side[89] = {
    0x42,0x1a, // prelude
    0x4c,0x5c,0x60, // names: side, self, value
    0x80,0x58,0x29,0x27,0x27,0x27,0x29,0x27,0x26,0x34, // code info
    0xb0, // LOAD_FAST 0
    0x57, // DUP_TOP
    0x13,0x42, // LOAD_ATTR 'num_sideset'
    0x81, // LOAD_CONST_SMALL_INT 1
    0xe5, // BINARY_OP 14 __iadd__
    0x5a, // ROT_TWO
    0x18,0x42, // STORE_ATTR 'num_sideset'
    0xb0, // LOAD_FAST 0
    0x13,0x40, // LOAD_ATTR 'pass_'
    0x80, // LOAD_CONST_SMALL_INT 0
    0xd8, // BINARY_OP 1 __gt__
    0x44,0x78, // POP_JUMP_IF_FALSE 56
    0xb0, // LOAD_FAST 0
    0x13,0x3d, // LOAD_ATTR 'sideset_count'
    0x80, // LOAD_CONST_SMALL_INT 0
    0xd9, // BINARY_OP 2 __eq__
    0x44,0x47, // POP_JUMP_IF_FALSE 7
    0x12,0x06, // LOAD_GLOBAL 'PIOASMError'
    0x10,0x4d, // LOAD_CONST_STRING 'no sideset'
    0x34,0x01, // CALL_FUNCTION 1
    0x65, // RAISE_OBJ
    0xb1, // LOAD_FAST 1
    0x81, // LOAD_CONST_SMALL_INT 1
    0xb0, // LOAD_FAST 0
    0x13,0x3d, // LOAD_ATTR 'sideset_count'
    0xf0, // BINARY_OP 25 __lshift__
    0xdb, // BINARY_OP 4 __ge__
    0x44,0x47, // POP_JUMP_IF_FALSE 7
    0x12,0x06, // LOAD_GLOBAL 'PIOASMError'
    0x23,0x03, // LOAD_CONST_OBJ 3
    0x34,0x01, // CALL_FUNCTION 1
    0x65, // RAISE_OBJ
    0x8d, // LOAD_CONST_SMALL_INT 13
    0xb0, // LOAD_FAST 0
    0x13,0x3d, // LOAD_ATTR 'sideset_count'
    0xf3, // BINARY_OP 28 __sub__
    0xc2, // STORE_FAST 2
    0xb0, // LOAD_FAST 0
    0x13,0x43, // LOAD_ATTR 'prog'
    0x80, // LOAD_CONST_SMALL_INT 0
    0x55, // LOAD_SUBSCR
    0x7f, // LOAD_CONST_SMALL_INT -1
    0x58, // DUP_TOP_TWO
    0x55, // LOAD_SUBSCR
    0xb0, // LOAD_FAST 0
    0x13,0x3e, // LOAD_ATTR 'sideset_opt'
    0x8c, // LOAD_CONST_SMALL_INT 12
    0xf0, // BINARY_OP 25 __lshift__
    0xb1, // LOAD_FAST 1
    0xb2, // LOAD_FAST 2
    0xf0, // BINARY_OP 25 __lshift__
    0xed, // BINARY_OP 22 __or__
    0xe0, // BINARY_OP 9 __ior__
    0x5b, // ROT_THREE
    0x56, // STORE_SUBSCR
    0xb0, // LOAD_FAST 0
    0x63, // RETURN_VALUE
};
#if MICROPY_PERSISTENT_CODE_SAVE
static const mp_raw_code_truncated_t proto_fun_rp2_PIOASMEmit_side = {
    .proto_fun_indicator[0] = MP_PROTO_FUN_INDICATOR_RAW_CODE_0,
    .proto_fun_indicator[1] = MP_PROTO_FUN_INDICATOR_RAW_CODE_1,
    .kind = MP_CODE_BYTECODE,
    .is_generator = 0,
    .fun_data = fun_data_rp2_PIOASMEmit_side,
    .children = NULL,
    #if MICROPY_PERSISTENT_CODE_SAVE
    .fun_data_len = 89,
    .n_children = 0,
    #if MICROPY_EMIT_MACHINE_CODE
    .prelude_offset = 0,
    #endif
    #if MICROPY_PY_SYS_SETTRACE
    .line_of_definition = 0,
    .prelude = {
        .n_state = 9,
        .n_exc_stack = 0,
        .scope_flags = 0,
        .n_pos_args = 2,
        .n_kwonly_args = 0,
        .n_def_pos_args = 0,
        .qstr_block_name_idx = 76,
        .line_info = fun_data_rp2_PIOASMEmit_side + 5,
        .line_info_top = fun_data_rp2_PIOASMEmit_side + 15,
        .opcodes = fun_data_rp2_PIOASMEmit_side + 15,
    },
    #endif
    #endif
};
#else
#define proto_fun_rp2_PIOASMEmit_side fun_data_rp2_PIOASMEmit_side[0]
#endif

// child of rp2_PIOASMEmit
// frozen bytecode for file rp2.py, scope rp2_PIOASMEmit_wrap_target
static const byte fun_data_rp2_PIOASMEmit_wrap_target[22] = {
    0x29,0x08, // prelude
    0x22,0x5c, // names: wrap_target, self
    0x80,0x63, // code info
    0xb0, // LOAD_FAST 0
    0x13,0x43, // LOAD_ATTR 'prog'
    0x83, // LOAD_CONST_SMALL_INT 3
    0x58, // DUP_TOP_TWO
    0x55, // LOAD_SUBSCR
    0xb0, // LOAD_FAST 0
    0x13,0x41, // LOAD_ATTR 'num_instr'
    0x87, // LOAD_CONST_SMALL_INT 7
    0xf0, // BINARY_OP 25 __lshift__
    0xe0, // BINARY_OP 9 __ior__
    0x5b, // ROT_THREE
    0x56, // STORE_SUBSCR
    0x51, // LOAD_CONST_NONE
    0x63, // RETURN_VALUE
};
#if MICROPY_PERSISTENT_CODE_SAVE
static const mp_raw_code_truncated_t proto_fun_rp2_PIOASMEmit_wrap_target = {
    .proto_fun_indicator[0] = MP_PROTO_FUN_INDICATOR_RAW_CODE_0,
    .proto_fun_indicator[1] = MP_PROTO_FUN_INDICATOR_RAW_CODE_1,
    .kind = MP_CODE_BYTECODE,
    .is_generator = 0,
    .fun_data = fun_data_rp2_PIOASMEmit_wrap_target,
    .children = NULL,
    #if MICROPY_PERSISTENT_CODE_SAVE
    .fun_data_len = 22,
    .n_children = 0,
    #if MICROPY_EMIT_MACHINE_CODE
    .prelude_offset = 0,
    #endif
    #if MICROPY_PY_SYS_SETTRACE
    .line_of_definition = 0,
    .prelude = {
        .n_state = 6,
        .n_exc_stack = 0,
        .scope_flags = 0,
        .n_pos_args = 1,
        .n_kwonly_args = 0,
        .n_def_pos_args = 0,
        .qstr_block_name_idx = 34,
        .line_info = fun_data_rp2_PIOASMEmit_wrap_target + 4,
        .line_info_top = fun_data_rp2_PIOASMEmit_wrap_target + 6,
        .opcodes = fun_data_rp2_PIOASMEmit_wrap_target + 6,
    },
    #endif
    #endif
};
#else
#define proto_fun_rp2_PIOASMEmit_wrap_target fun_data_rp2_PIOASMEmit_wrap_target[0]
#endif

// child of rp2_PIOASMEmit
// frozen bytecode for file rp2.py, scope rp2_PIOASMEmit_wrap
static const byte fun_data_rp2_PIOASMEmit_wrap[38] = {
    0x29,0x0c, // prelude
    0x23,0x5c, // names: wrap, self
    0x80,0x66,0x28,0x30, // code info
    0xb0, // LOAD_FAST 0
    0x13,0x41, // LOAD_ATTR 'num_instr'
    0x43,0x43, // POP_JUMP_IF_TRUE 3
    0x12,0x4e, // LOAD_GLOBAL 'AssertionError'
    0x65, // RAISE_OBJ
    0xb0, // LOAD_FAST 0
    0x13,0x43, // LOAD_ATTR 'prog'
    0x83, // LOAD_CONST_SMALL_INT 3
    0x58, // DUP_TOP_TWO
    0x55, // LOAD_SUBSCR
    0xb0, // LOAD_FAST 0
    0x13,0x41, // LOAD_ATTR 'num_instr'
    0x81, // LOAD_CONST_SMALL_INT 1
    0xf3, // BINARY_OP 28 __sub__
    0x8c, // LOAD_CONST_SMALL_INT 12
    0xf0, // BINARY_OP 25 __lshift__
    0xe0, // BINARY_OP 9 __ior__
    0x5b, // ROT_THREE
    0x56, // STORE_SUBSCR
    0x52, // LOAD_CONST_TRUE
    0xb0, // LOAD_FAST 0
    0x18,0x48, // STORE_ATTR 'wrap_used'
    0x51, // LOAD_CONST_NONE
    0x63, // RETURN_VALUE
};
#if MICROPY_PERSISTENT_CODE_SAVE
static const mp_raw_code_truncated_t proto_fun_rp2_PIOASMEmit_wrap = {
    .proto_fun_indicator[0] = MP_PROTO_FUN_INDICATOR_RAW_CODE_0,
    .proto_fun_indicator[1] = MP_PROTO_FUN_INDICATOR_RAW_CODE_1,
    .kind = MP_CODE_BYTECODE,
    .is_generator = 0,
    .fun_data = fun_data_rp2_PIOASMEmit_wrap,
    .children = NULL,
    #if MICROPY_PERSISTENT_CODE_SAVE
    .fun_data_len = 38,
    .n_children = 0,
    #if MICROPY_EMIT_MACHINE_CODE
    .prelude_offset = 0,
    #endif
    #if MICROPY_PY_SYS_SETTRACE
    .line_of_definition = 0,
    .prelude = {
        .n_state = 6,
        .n_exc_stack = 0,
        .scope_flags = 0,
        .n_pos_args = 1,
        .n_kwonly_args = 0,
        .n_def_pos_args = 0,
        .qstr_block_name_idx = 35,
        .line_info = fun_data_rp2_PIOASMEmit_wrap + 4,
        .line_info_top = fun_data_rp2_PIOASMEmit_wrap + 8,
        .opcodes = fun_data_rp2_PIOASMEmit_wrap + 8,
    },
    #endif
    #endif
};
#else
#define proto_fun_rp2_PIOASMEmit_wrap fun_data_rp2_PIOASMEmit_wrap[0]
#endif

// child of rp2_PIOASMEmit
// frozen bytecode for file rp2.py, scope rp2_PIOASMEmit_label
static const byte fun_data_rp2_PIOASMEmit_label[46] = {
    0x2a,0x10, // prelude
    0x24,0x5c,0x24, // names: label, self, label
    0x80,0x6b,0x27,0x27,0x2c, // code info
    0xb0, // LOAD_FAST 0
    0x13,0x40, // LOAD_ATTR 'pass_'
    0x80, // LOAD_CONST_SMALL_INT 0
    0xd9, // BINARY_OP 2 __eq__
    0x44,0x5b, // POP_JUMP_IF_FALSE 27
    0xb1, // LOAD_FAST 1
    0xb0, // LOAD_FAST 0
    0x13,0x46, // LOAD_ATTR 'labels'
    0xdd, // BINARY_OP 6 <in>
    0x44,0x4c, // POP_JUMP_IF_FALSE 12
    0x12,0x06, // LOAD_GLOBAL 'PIOASMError'
    0x23,0x04, // LOAD_CONST_OBJ 4
    0x14,0x4f, // LOAD_METHOD 'format'
    0xb1, // LOAD_FAST 1
    0x36,0x01, // CALL_METHOD 1
    0x34,0x01, // CALL_FUNCTION 1
    0x65, // RAISE_OBJ
    0xb0, // LOAD_FAST 0
    0x13,0x41, // LOAD_ATTR 'num_instr'
    0xb0, // LOAD_FAST 0
    0x13,0x46, // LOAD_ATTR 'labels'
    0xb1, // LOAD_FAST 1
    0x56, // STORE_SUBSCR
    0x51, // LOAD_CONST_NONE
    0x63, // RETURN_VALUE
};
#if MICROPY_PERSISTENT_CODE_SAVE
static const mp_raw_code_truncated_t proto_fun_rp2_PIOASMEmit_label = {
    .proto_fun_indicator[0] = MP_PROTO_FUN_INDICATOR_RAW_CODE_0,
    .proto_fun_indicator[1] = MP_PROTO_FUN_INDICATOR_RAW_CODE_1,
    .kind = MP_CODE_BYTECODE,
    .is_generator = 0,
    .fun_data = fun_data_rp2_PIOASMEmit_label,
    .children = NULL,
    #if MICROPY_PERSISTENT_CODE_SAVE
    .fun_data_len = 46,
    .n_children = 0,
    #if MICROPY_EMIT_MACHINE_CODE
    .prelude_offset = 0,
    #endif
    #if MICROPY_PY_SYS_SETTRACE
    .line_of_definition = 0,
    .prelude = {
        .n_state = 6,
        .n_exc_stack = 0,
        .scope_flags = 0,
        .n_pos_args = 2,
        .n_kwonly_args = 0,
        .n_def_pos_args = 0,
        .qstr_block_name_idx = 36,
        .line_info = fun_data_rp2_PIOASMEmit_label + 5,
        .line_info_top = fun_data_rp2_PIOASMEmit_label + 10,
        .opcodes = fun_data_rp2_PIOASMEmit_label + 10,
    },
    #endif
    #endif
};
#else
#define proto_fun_rp2_PIOASMEmit_label fun_data_rp2_PIOASMEmit_label[0]
#endif

// child of rp2_PIOASMEmit
// frozen bytecode for file rp2.py, scope rp2_PIOASMEmit_word
static const byte fun_data_rp2_PIOASMEmit_word[83] = {
    0xb3,0x01,0x1c, // prelude
    0x25,0x5c,0x5a,0x24, // names: word, self, instr, label
    0x80,0x71,0x29,0x27,0x25,0x44,0x28,0x2c,0x26,0x2d, // code info
    0xb0, // LOAD_FAST 0
    0x57, // DUP_TOP
    0x13,0x41, // LOAD_ATTR 'num_instr'
    0x81, // LOAD_CONST_SMALL_INT 1
    0xe5, // BINARY_OP 14 __iadd__
    0x5a, // ROT_TWO
    0x18,0x41, // STORE_ATTR 'num_instr'
    0xb0, // LOAD_FAST 0
    0x13,0x40, // LOAD_ATTR 'pass_'
    0x80, // LOAD_CONST_SMALL_INT 0
    0xd8, // BINARY_OP 1 __gt__
    0x44,0x70, // POP_JUMP_IF_FALSE 48
    0xb2, // LOAD_FAST 2
    0x51, // LOAD_CONST_NONE
    0xde, // BINARY_OP 7 <is>
    0x44,0x44, // POP_JUMP_IF_FALSE 4
    0x80, // LOAD_CONST_SMALL_INT 0
    0xc2, // STORE_FAST 2
    0x42,0x5a, // JUMP 26
    0xb2, // LOAD_FAST 2
    0xb0, // LOAD_FAST 0
    0x13,0x46, // LOAD_ATTR 'labels'
    0xdd, // BINARY_OP 6 <in>
    0xd3, // UNARY_OP 3 <not>
    0x44,0x4c, // POP_JUMP_IF_FALSE 12
    0x12,0x06, // LOAD_GLOBAL 'PIOASMError'
    0x23,0x05, // LOAD_CONST_OBJ 5
    0x14,0x4f, // LOAD_METHOD 'format'
    0xb2, // LOAD_FAST 2
    0x36,0x01, // CALL_METHOD 1
    0x34,0x01, // CALL_FUNCTION 1
    0x65, // RAISE_OBJ
    0xb0, // LOAD_FAST 0
    0x13,0x46, // LOAD_ATTR 'labels'
    0xb2, // LOAD_FAST 2
    0x55, // LOAD_SUBSCR
    0xc2, // STORE_FAST 2
    0xb0, // LOAD_FAST 0
    0x13,0x43, // LOAD_ATTR 'prog'
    0x80, // LOAD_CONST_SMALL_INT 0
    0x55, // LOAD_SUBSCR
    0x14,0x50, // LOAD_METHOD 'append'
    0xb1, // LOAD_FAST 1
    0xb2, // LOAD_FAST 2
    0xed, // BINARY_OP 22 __or__
    0x36,0x01, // CALL_METHOD 1
    0x59, // POP_TOP
    0xb0, // LOAD_FAST 0
    0x63, // RETURN_VALUE
};
#if MICROPY_PERSISTENT_CODE_SAVE
static const mp_raw_code_truncated_t proto_fun_rp2_PIOASMEmit_word = {
    .proto_fun_indicator[0] = MP_PROTO_FUN_INDICATOR_RAW_CODE_0,
    .proto_fun_indicator[1] = MP_PROTO_FUN_INDICATOR_RAW_CODE_1,
    .kind = MP_CODE_BYTECODE,
    .is_generator = 0,
    .fun_data = fun_data_rp2_PIOASMEmit_word,
    .children = NULL,
    #if MICROPY_PERSISTENT_CODE_SAVE
    .fun_data_len = 83,
    .n_children = 0,
    #if MICROPY_EMIT_MACHINE_CODE
    .prelude_offset = 0,
    #endif
    #if MICROPY_PY_SYS_SETTRACE
    .line_of_definition = 0,
    .prelude = {
        .n_state = 7,
        .n_exc_stack = 0,
        .scope_flags = 0,
        .n_pos_args = 3,
        .n_kwonly_args = 0,
        .n_def_pos_args = 1,
        .qstr_block_name_idx = 37,
        .line_info = fun_data_rp2_PIOASMEmit_word + 7,
        .line_info_top = fun_data_rp2_PIOASMEmit_word + 17,
        .opcodes = fun_data_rp2_PIOASMEmit_word + 17,
    },
    #endif
    #endif
};
#else
#define proto_fun_rp2_PIOASMEmit_word fun_data_rp2_PIOASMEmit_word[0]
#endif

// child of rp2_PIOASMEmit
// frozen bytecode for file rp2.py, scope rp2_PIOASMEmit_nop
static const byte fun_data_rp2_PIOASMEmit_nop[16] = {
    0x19,0x08, // prelude
    0x26,0x5c, // names: nop, self
    0x80,0x7d, // code info
    0xb0, // LOAD_FAST 0
    0x14,0x25, // LOAD_METHOD 'word'
    0x22,0x82,0xc0,0x42, // LOAD_CONST_SMALL_INT 41026
    0x36,0x01, // CALL_METHOD 1
    0x63, // RETURN_VALUE
};
#if MICROPY_PERSISTENT_CODE_SAVE
static const mp_raw_code_truncated_t proto_fun_rp2_PIOASMEmit_nop = {
    .proto_fun_indicator[0] = MP_PROTO_FUN_INDICATOR_RAW_CODE_0,
    .proto_fun_indicator[1] = MP_PROTO_FUN_INDICATOR_RAW_CODE_1,
    .kind = MP_CODE_BYTECODE,
    .is_generator = 0,
    .fun_data = fun_data_rp2_PIOASMEmit_nop,
    .children = NULL,
    #if MICROPY_PERSISTENT_CODE_SAVE
    .fun_data_len = 16,
    .n_children = 0,
    #if MICROPY_EMIT_MACHINE_CODE
    .prelude_offset = 0,
    #endif
    #if MICROPY_PY_SYS_SETTRACE
    .line_of_definition = 0,
    .prelude = {
        .n_state = 4,
        .n_exc_stack = 0,
        .scope_flags = 0,
        .n_pos_args = 1,
        .n_kwonly_args = 0,
        .n_def_pos_args = 0,
        .qstr_block_name_idx = 38,
        .line_info = fun_data_rp2_PIOASMEmit_nop + 4,
        .line_info_top = fun_data_rp2_PIOASMEmit_nop + 6,
        .opcodes = fun_data_rp2_PIOASMEmit_nop + 6,
    },
    #endif
    #endif
};
#else
#define proto_fun_rp2_PIOASMEmit_nop fun_data_rp2_PIOASMEmit_nop[0]
#endif

// child of rp2_PIOASMEmit
// frozen bytecode for file rp2.py, scope rp2_PIOASMEmit_jmp
static const byte fun_data_rp2_PIOASMEmit_jmp[33] = {
    0xbb,0x01,0x12, // prelude
    0x27,0x5c,0x61,0x24, // names: jmp, self, cond, label
    0x80,0x80,0x25,0x22,0x22, // code info
    0xb2, // LOAD_FAST 2
    0x51, // LOAD_CONST_NONE
    0xde, // BINARY_OP 7 <is>
    0x44,0x44, // POP_JUMP_IF_FALSE 4
    0xb1, // LOAD_FAST 1
    0xc2, // STORE_FAST 2
    0x80, // LOAD_CONST_SMALL_INT 0
    0xc1, // STORE_FAST 1
    0xb0, // LOAD_FAST 0
    0x14,0x25, // LOAD_METHOD 'word'
    0x80, // LOAD_CONST_SMALL_INT 0
    0xb1, // LOAD_FAST 1
    0x85, // LOAD_CONST_SMALL_INT 5
    0xf0, // BINARY_OP 25 __lshift__
    0xed, // BINARY_OP 22 __or__
    0xb2, // LOAD_FAST 2
    0x36,0x02, // CALL_METHOD 2
    0x63, // RETURN_VALUE
};
#if MICROPY_PERSISTENT_CODE_SAVE
static const mp_raw_code_truncated_t proto_fun_rp2_PIOASMEmit_jmp = {
    .proto_fun_indicator[0] = MP_PROTO_FUN_INDICATOR_RAW_CODE_0,
    .proto_fun_indicator[1] = MP_PROTO_FUN_INDICATOR_RAW_CODE_1,
    .kind = MP_CODE_BYTECODE,
    .is_generator = 0,
    .fun_data = fun_data_rp2_PIOASMEmit_jmp,
    .children = NULL,
    #if MICROPY_PERSISTENT_CODE_SAVE
    .fun_data_len = 33,
    .n_children = 0,
    #if MICROPY_EMIT_MACHINE_CODE
    .prelude_offset = 0,
    #endif
    #if MICROPY_PY_SYS_SETTRACE
    .line_of_definition = 0,
    .prelude = {
        .n_state = 8,
        .n_exc_stack = 0,
        .scope_flags = 0,
        .n_pos_args = 3,
        .n_kwonly_args = 0,
        .n_def_pos_args = 1,
        .qstr_block_name_idx = 39,
        .line_info = fun_data_rp2_PIOASMEmit_jmp + 7,
        .line_info_top = fun_data_rp2_PIOASMEmit_jmp + 12,
        .opcodes = fun_data_rp2_PIOASMEmit_jmp + 12,
    },
    #endif
    #endif
};
#else
#define proto_fun_rp2_PIOASMEmit_jmp fun_data_rp2_PIOASMEmit_jmp[0]
#endif

// child of rp2_PIOASMEmit
// frozen bytecode for file rp2.py, scope rp2_PIOASMEmit_wait
static const byte fun_data_rp2_PIOASMEmit_wait[52] = {
    0xc0,0x04,0x16, // prelude
    0x28,0x5c,0x62,0x63,0x64, // names: wait, self, polarity, src, index
    0x80,0x86,0x25,0x24,0x25,0x24, // code info
    0xb2, // LOAD_FAST 2
    0x86, // LOAD_CONST_SMALL_INT 6
    0xd9, // BINARY_OP 2 __eq__
    0x44,0x44, // POP_JUMP_IF_FALSE 4
    0x81, // LOAD_CONST_SMALL_INT 1
    0xc2, // STORE_FAST 2
    0x42,0x49, // JUMP 9
    0xb2, // LOAD_FAST 2
    0x80, // LOAD_CONST_SMALL_INT 0
    0xdc, // BINARY_OP 5 __ne__
    0x44,0x44, // POP_JUMP_IF_FALSE 4
    0x82, // LOAD_CONST_SMALL_INT 2
    0xc2, // STORE_FAST 2
    0x42,0x40, // JUMP 0
    0xb0, // LOAD_FAST 0
    0x14,0x25, // LOAD_METHOD 'word'
    0x22,0x80,0xc0,0x00, // LOAD_CONST_SMALL_INT 8192
    0xb1, // LOAD_FAST 1
    0x87, // LOAD_CONST_SMALL_INT 7
    0xf0, // BINARY_OP 25 __lshift__
    0xed, // BINARY_OP 22 __or__
    0xb2, // LOAD_FAST 2
    0x85, // LOAD_CONST_SMALL_INT 5
    0xf0, // BINARY_OP 25 __lshift__
    0xed, // BINARY_OP 22 __or__
    0xb3, // LOAD_FAST 3
    0xed, // BINARY_OP 22 __or__
    0x36,0x01, // CALL_METHOD 1
    0x63, // RETURN_VALUE
};
#if MICROPY_PERSISTENT_CODE_SAVE
static const mp_raw_code_truncated_t proto_fun_rp2_PIOASMEmit_wait = {
    .proto_fun_indicator[0] = MP_PROTO_FUN_INDICATOR_RAW_CODE_0,
    .proto_fun_indicator[1] = MP_PROTO_FUN_INDICATOR_RAW_CODE_1,
    .kind = MP_CODE_BYTECODE,
    .is_generator = 0,
    .fun_data = fun_data_rp2_PIOASMEmit_wait,
    .children = NULL,
    #if MICROPY_PERSISTENT_CODE_SAVE
    .fun_data_len = 52,
    .n_children = 0,
    #if MICROPY_EMIT_MACHINE_CODE
    .prelude_offset = 0,
    #endif
    #if MICROPY_PY_SYS_SETTRACE
    .line_of_definition = 0,
    .prelude = {
        .n_state = 9,
        .n_exc_stack = 0,
        .scope_flags = 0,
        .n_pos_args = 4,
        .n_kwonly_args = 0,
        .n_def_pos_args = 0,
        .qstr_block_name_idx = 40,
        .line_info = fun_data_rp2_PIOASMEmit_wait + 8,
        .line_info_top = fun_data_rp2_PIOASMEmit_wait + 14,
        .opcodes = fun_data_rp2_PIOASMEmit_wait + 14,
    },
    #endif
    #endif
};
#else
#define proto_fun_rp2_PIOASMEmit_wait fun_data_rp2_PIOASMEmit_wait[0]
#endif

// child of rp2_PIOASMEmit
// frozen bytecode for file rp2.py, scope rp2_PIOASMEmit_in_
static const byte fun_data_rp2_PIOASMEmit_in_[55] = {
    0x3b,0x10, // prelude
    0x29,0x5c,0x63,0x65, // names: in_, self, src, data
    0x80,0x8d,0x2f,0x2c, // code info
    0x80, // LOAD_CONST_SMALL_INT 0
    0xb2, // LOAD_FAST 2
    0x57, // DUP_TOP
    0x5b, // ROT_THREE
    0xd7, // BINARY_OP 0 __lt__
    0x46,0x04, // JUMP_IF_FALSE_OR_POP 4
    0xa0, // LOAD_CONST_SMALL_INT 32
    0xda, // BINARY_OP 3 __le__
    0x42,0x42, // JUMP 2
    0x5a, // ROT_TWO
    0x59, // POP_TOP
    0x43,0x4c, // POP_JUMP_IF_TRUE 12
    0x12,0x06, // LOAD_GLOBAL 'PIOASMError'
    0x23,0x06, // LOAD_CONST_OBJ 6
    0x14,0x4f, // LOAD_METHOD 'format'
    0xb2, // LOAD_FAST 2
    0x36,0x01, // CALL_METHOD 1
    0x34,0x01, // CALL_FUNCTION 1
    0x65, // RAISE_OBJ
    0xb0, // LOAD_FAST 0
    0x14,0x25, // LOAD_METHOD 'word'
    0x22,0x81,0x80,0x00, // LOAD_CONST_SMALL_INT 16384
    0xb1, // LOAD_FAST 1
    0x85, // LOAD_CONST_SMALL_INT 5
    0xf0, // BINARY_OP 25 __lshift__
    0xed, // BINARY_OP 22 __or__
    0xb2, // LOAD_FAST 2
    0x9f, // LOAD_CONST_SMALL_INT 31
    0xef, // BINARY_OP 24 __and__
    0xed, // BINARY_OP 22 __or__
    0x36,0x01, // CALL_METHOD 1
    0x63, // RETURN_VALUE
};
#if MICROPY_PERSISTENT_CODE_SAVE
static const mp_raw_code_truncated_t proto_fun_rp2_PIOASMEmit_in_ = {
    .proto_fun_indicator[0] = MP_PROTO_FUN_INDICATOR_RAW_CODE_0,
    .proto_fun_indicator[1] = MP_PROTO_FUN_INDICATOR_RAW_CODE_1,
    .kind = MP_CODE_BYTECODE,
    .is_generator = 0,
    .fun_data = fun_data_rp2_PIOASMEmit_in_,
    .children = NULL,
    #if MICROPY_PERSISTENT_CODE_SAVE
    .fun_data_len = 55,
    .n_children = 0,
    #if MICROPY_EMIT_MACHINE_CODE
    .prelude_offset = 0,
    #endif
    #if MICROPY_PY_SYS_SETTRACE
    .line_of_definition = 0,
    .prelude = {
        .n_state = 8,
        .n_exc_stack = 0,
        .scope_flags = 0,
        .n_pos_args = 3,
        .n_kwonly_args = 0,
        .n_def_pos_args = 0,
        .qstr_block_name_idx = 41,
        .line_info = fun_data_rp2_PIOASMEmit_in_ + 6,
        .line_info_top = fun_data_rp2_PIOASMEmit_in_ + 10,
        .opcodes = fun_data_rp2_PIOASMEmit_in_ + 10,
    },
    #endif
    #endif
};
#else
#define proto_fun_rp2_PIOASMEmit_in_ fun_data_rp2_PIOASMEmit_in_[0]
#endif

// child of rp2_PIOASMEmit
// frozen bytecode for file rp2.py, scope rp2_PIOASMEmit_out
static const byte fun_data_rp2_PIOASMEmit_out[64] = {
    0x3b,0x14, // prelude
    0x2a,0x5c,0x66,0x65, // names: out, self, dest, data
    0x80,0x92,0x25,0x22,0x2f,0x2c, // code info
    0xb1, // LOAD_FAST 1
    0x88, // LOAD_CONST_SMALL_INT 8
    0xd9, // BINARY_OP 2 __eq__
    0x44,0x42, // POP_JUMP_IF_FALSE 2
    0x87, // LOAD_CONST_SMALL_INT 7
    0xc1, // STORE_FAST 1
    0x80, // LOAD_CONST_SMALL_INT 0
    0xb2, // LOAD_FAST 2
    0x57, // DUP_TOP
    0x5b, // ROT_THREE
    0xd7, // BINARY_OP 0 __lt__
    0x46,0x04, // JUMP_IF_FALSE_OR_POP 4
    0xa0, // LOAD_CONST_SMALL_INT 32
    0xda, // BINARY_OP 3 __le__
    0x42,0x42, // JUMP 2
    0x5a, // ROT_TWO
    0x59, // POP_TOP
    0x43,0x4c, // POP_JUMP_IF_TRUE 12
    0x12,0x06, // LOAD_GLOBAL 'PIOASMError'
    0x23,0x06, // LOAD_CONST_OBJ 6
    0x14,0x4f, // LOAD_METHOD 'format'
    0xb2, // LOAD_FAST 2
    0x36,0x01, // CALL_METHOD 1
    0x34,0x01, // CALL_FUNCTION 1
    0x65, // RAISE_OBJ
    0xb0, // LOAD_FAST 0
    0x14,0x25, // LOAD_METHOD 'word'
    0x22,0x81,0xc0,0x00, // LOAD_CONST_SMALL_INT 24576
    0xb1, // LOAD_FAST 1
    0x85, // LOAD_CONST_SMALL_INT 5
    0xf0, // BINARY_OP 25 __lshift__
    0xed, // BINARY_OP 22 __or__
    0xb2, // LOAD_FAST 2
    0x9f, // LOAD_CONST_SMALL_INT 31
    0xef, // BINARY_OP 24 __and__
    0xed, // BINARY_OP 22 __or__
    0x36,0x01, // CALL_METHOD 1
    0x63, // RETURN_VALUE
};
#if MICROPY_PERSISTENT_CODE_SAVE
static const mp_raw_code_truncated_t proto_fun_rp2_PIOASMEmit_out = {
    .proto_fun_indicator[0] = MP_PROTO_FUN_INDICATOR_RAW_CODE_0,
    .proto_fun_indicator[1] = MP_PROTO_FUN_INDICATOR_RAW_CODE_1,
    .kind = MP_CODE_BYTECODE,
    .is_generator = 0,
    .fun_data = fun_data_rp2_PIOASMEmit_out,
    .children = NULL,
    #if MICROPY_PERSISTENT_CODE_SAVE
    .fun_data_len = 64,
    .n_children = 0,
    #if MICROPY_EMIT_MACHINE_CODE
    .prelude_offset = 0,
    #endif
    #if MICROPY_PY_SYS_SETTRACE
    .line_of_definition = 0,
    .prelude = {
        .n_state = 8,
        .n_exc_stack = 0,
        .scope_flags = 0,
        .n_pos_args = 3,
        .n_kwonly_args = 0,
        .n_def_pos_args = 0,
        .qstr_block_name_idx = 42,
        .line_info = fun_data_rp2_PIOASMEmit_out + 6,
        .line_info_top = fun_data_rp2_PIOASMEmit_out + 12,
        .opcodes = fun_data_rp2_PIOASMEmit_out + 12,
    },
    #endif
    #endif
};
#else
#define proto_fun_rp2_PIOASMEmit_out fun_data_rp2_PIOASMEmit_out[0]
#endif

// child of rp2_PIOASMEmit
// frozen bytecode for file rp2.py, scope rp2_PIOASMEmit_push
static const byte fun_data_rp2_PIOASMEmit_push[42] = {
    0xbb,0x80,0x01,0x12, // prelude
    0x2b,0x5c,0x60,0x67, // names: push, self, value, value2
    0x80,0x99,0x24,0x25,0x24, // code info
    0xb1, // LOAD_FAST 1
    0xb2, // LOAD_FAST 2
    0xe0, // BINARY_OP 9 __ior__
    0xc1, // STORE_FAST 1
    0xb1, // LOAD_FAST 1
    0x81, // LOAD_CONST_SMALL_INT 1
    0xef, // BINARY_OP 24 __and__
    0x43,0x44, // POP_JUMP_IF_TRUE 4
    0xb1, // LOAD_FAST 1
    0xa0, // LOAD_CONST_SMALL_INT 32
    0xe0, // BINARY_OP 9 __ior__
    0xc1, // STORE_FAST 1
    0xb0, // LOAD_FAST 0
    0x14,0x25, // LOAD_METHOD 'word'
    0x22,0x82,0x80,0x00, // LOAD_CONST_SMALL_INT 32768
    0xb1, // LOAD_FAST 1
    0x22,0x80,0x60, // LOAD_CONST_SMALL_INT 96
    0xef, // BINARY_OP 24 __and__
    0xed, // BINARY_OP 22 __or__
    0x36,0x01, // CALL_METHOD 1
    0x63, // RETURN_VALUE
};
#if MICROPY_PERSISTENT_CODE_SAVE
static const mp_raw_code_truncated_t proto_fun_rp2_PIOASMEmit_push = {
    .proto_fun_indicator[0] = MP_PROTO_FUN_INDICATOR_RAW_CODE_0,
    .proto_fun_indicator[1] = MP_PROTO_FUN_INDICATOR_RAW_CODE_1,
    .kind = MP_CODE_BYTECODE,
    .is_generator = 0,
    .fun_data = fun_data_rp2_PIOASMEmit_push,
    .children = NULL,
    #if MICROPY_PERSISTENT_CODE_SAVE
    .fun_data_len = 42,
    .n_children = 0,
    #if MICROPY_EMIT_MACHINE_CODE
    .prelude_offset = 0,
    #endif
    #if MICROPY_PY_SYS_SETTRACE
    .line_of_definition = 0,
    .prelude = {
        .n_state = 8,
        .n_exc_stack = 0,
        .scope_flags = 0,
        .n_pos_args = 3,
        .n_kwonly_args = 0,
        .n_def_pos_args = 2,
        .qstr_block_name_idx = 43,
        .line_info = fun_data_rp2_PIOASMEmit_push + 8,
        .line_info_top = fun_data_rp2_PIOASMEmit_push + 13,
        .opcodes = fun_data_rp2_PIOASMEmit_push + 13,
    },
    #endif
    #endif
};
#else
#define proto_fun_rp2_PIOASMEmit_push fun_data_rp2_PIOASMEmit_push[0]
#endif

// child of rp2_PIOASMEmit
// frozen bytecode for file rp2.py, scope rp2_PIOASMEmit_pull
static const byte fun_data_rp2_PIOASMEmit_pull[42] = {
    0xbb,0x80,0x01,0x12, // prelude
    0x2c,0x5c,0x60,0x67, // names: pull, self, value, value2
    0x80,0x9f,0x24,0x25,0x24, // code info
    0xb1, // LOAD_FAST 1
    0xb2, // LOAD_FAST 2
    0xe0, // BINARY_OP 9 __ior__
    0xc1, // STORE_FAST 1
    0xb1, // LOAD_FAST 1
    0x81, // LOAD_CONST_SMALL_INT 1
    0xef, // BINARY_OP 24 __and__
    0x43,0x44, // POP_JUMP_IF_TRUE 4
    0xb1, // LOAD_FAST 1
    0xa0, // LOAD_CONST_SMALL_INT 32
    0xe0, // BINARY_OP 9 __ior__
    0xc1, // STORE_FAST 1
    0xb0, // LOAD_FAST 0
    0x14,0x25, // LOAD_METHOD 'word'
    0x22,0x82,0x81,0x00, // LOAD_CONST_SMALL_INT 32896
    0xb1, // LOAD_FAST 1
    0x22,0x80,0x60, // LOAD_CONST_SMALL_INT 96
    0xef, // BINARY_OP 24 __and__
    0xed, // BINARY_OP 22 __or__
    0x36,0x01, // CALL_METHOD 1
    0x63, // RETURN_VALUE
};
#if MICROPY_PERSISTENT_CODE_SAVE
static const mp_raw_code_truncated_t proto_fun_rp2_PIOASMEmit_pull = {
    .proto_fun_indicator[0] = MP_PROTO_FUN_INDICATOR_RAW_CODE_0,
    .proto_fun_indicator[1] = MP_PROTO_FUN_INDICATOR_RAW_CODE_1,
    .kind = MP_CODE_BYTECODE,
    .is_generator = 0,
    .fun_data = fun_data_rp2_PIOASMEmit_pull,
    .children = NULL,
    #if MICROPY_PERSISTENT_CODE_SAVE
    .fun_data_len = 42,
    .n_children = 0,
    #if MICROPY_EMIT_MACHINE_CODE
    .prelude_offset = 0,
    #endif
    #if MICROPY_PY_SYS_SETTRACE
    .line_of_definition = 0,
    .prelude = {
        .n_state = 8,
        .n_exc_stack = 0,
        .scope_flags = 0,
        .n_pos_args = 3,
        .n_kwonly_args = 0,
        .n_def_pos_args = 2,
        .qstr_block_name_idx = 44,
        .line_info = fun_data_rp2_PIOASMEmit_pull + 8,
        .line_info_top = fun_data_rp2_PIOASMEmit_pull + 13,
        .opcodes = fun_data_rp2_PIOASMEmit_pull + 13,
    },
    #endif
    #endif
};
#else
#define proto_fun_rp2_PIOASMEmit_pull fun_data_rp2_PIOASMEmit_pull[0]
#endif

// child of rp2_PIOASMEmit
// frozen bytecode for file rp2.py, scope rp2_PIOASMEmit_mov
static const byte fun_data_rp2_PIOASMEmit_mov[33] = {
    0x3b,0x10, // prelude
    0x2d,0x5c,0x66,0x63, // names: mov, self, dest, src
    0x80,0xa5,0x25,0x22, // code info
    0xb1, // LOAD_FAST 1
    0x88, // LOAD_CONST_SMALL_INT 8
    0xd9, // BINARY_OP 2 __eq__
    0x44,0x42, // POP_JUMP_IF_FALSE 2
    0x84, // LOAD_CONST_SMALL_INT 4
    0xc1, // STORE_FAST 1
    0xb0, // LOAD_FAST 0
    0x14,0x25, // LOAD_METHOD 'word'
    0x22,0x82,0xc0,0x00, // LOAD_CONST_SMALL_INT 40960
    0xb1, // LOAD_FAST 1
    0x85, // LOAD_CONST_SMALL_INT 5
    0xf0, // BINARY_OP 25 __lshift__
    0xed, // BINARY_OP 22 __or__
    0xb2, // LOAD_FAST 2
    0xed, // BINARY_OP 22 __or__
    0x36,0x01, // CALL_METHOD 1
    0x63, // RETURN_VALUE
};
#if MICROPY_PERSISTENT_CODE_SAVE
static const mp_raw_code_truncated_t proto_fun_rp2_PIOASMEmit_mov = {
    .proto_fun_indicator[0] = MP_PROTO_FUN_INDICATOR_RAW_CODE_0,
    .proto_fun_indicator[1] = MP_PROTO_FUN_INDICATOR_RAW_CODE_1,
    .kind = MP_CODE_BYTECODE,
    .is_generator = 0,
    .fun_data = fun_data_rp2_PIOASMEmit_mov,
    .children = NULL,
    #if MICROPY_PERSISTENT_CODE_SAVE
    .fun_data_len = 33,
    .n_children = 0,
    #if MICROPY_EMIT_MACHINE_CODE
    .prelude_offset = 0,
    #endif
    #if MICROPY_PY_SYS_SETTRACE
    .line_of_definition = 0,
    .prelude = {
        .n_state = 8,
        .n_exc_stack = 0,
        .scope_flags = 0,
        .n_pos_args = 3,
        .n_kwonly_args = 0,
        .n_def_pos_args = 0,
        .qstr_block_name_idx = 45,
        .line_info = fun_data_rp2_PIOASMEmit_mov + 6,
        .line_info_top = fun_data_rp2_PIOASMEmit_mov + 10,
        .opcodes = fun_data_rp2_PIOASMEmit_mov + 10,
    },
    #endif
    #endif
};
#else
#define proto_fun_rp2_PIOASMEmit_mov fun_data_rp2_PIOASMEmit_mov[0]
#endif

// child of rp2_PIOASMEmit
// frozen bytecode for file rp2.py, scope rp2_PIOASMEmit_irq
static const byte fun_data_rp2_PIOASMEmit_irq[39] = {
    0xbb,0x01,0x12, // prelude
    0x2e,0x5c,0x68,0x64, // names: irq, self, mod, index
    0x80,0xaa,0x25,0x22,0x22, // code info
    0xb2, // LOAD_FAST 2
    0x51, // LOAD_CONST_NONE
    0xde, // BINARY_OP 7 <is>
    0x44,0x44, // POP_JUMP_IF_FALSE 4
    0xb1, // LOAD_FAST 1
    0xc2, // STORE_FAST 2
    0x80, // LOAD_CONST_SMALL_INT 0
    0xc1, // STORE_FAST 1
    0xb0, // LOAD_FAST 0
    0x14,0x25, // LOAD_METHOD 'word'
    0x22,0x83,0x80,0x00, // LOAD_CONST_SMALL_INT 49152
    0xb1, // LOAD_FAST 1
    0x22,0x80,0x60, // LOAD_CONST_SMALL_INT 96
    0xef, // BINARY_OP 24 __and__
    0xed, // BINARY_OP 22 __or__
    0xb2, // LOAD_FAST 2
    0xed, // BINARY_OP 22 __or__
    0x36,0x01, // CALL_METHOD 1
    0x63, // RETURN_VALUE
};
#if MICROPY_PERSISTENT_CODE_SAVE
static const mp_raw_code_truncated_t proto_fun_rp2_PIOASMEmit_irq = {
    .proto_fun_indicator[0] = MP_PROTO_FUN_INDICATOR_RAW_CODE_0,
    .proto_fun_indicator[1] = MP_PROTO_FUN_INDICATOR_RAW_CODE_1,
    .kind = MP_CODE_BYTECODE,
    .is_generator = 0,
    .fun_data = fun_data_rp2_PIOASMEmit_irq,
    .children = NULL,
    #if MICROPY_PERSISTENT_CODE_SAVE
    .fun_data_len = 39,
    .n_children = 0,
    #if MICROPY_EMIT_MACHINE_CODE
    .prelude_offset = 0,
    #endif
    #if MICROPY_PY_SYS_SETTRACE
    .line_of_definition = 0,
    .prelude = {
        .n_state = 8,
        .n_exc_stack = 0,
        .scope_flags = 0,
        .n_pos_args = 3,
        .n_kwonly_args = 0,
        .n_def_pos_args = 1,
        .qstr_block_name_idx = 46,
        .line_info = fun_data_rp2_PIOASMEmit_irq + 7,
        .line_info_top = fun_data_rp2_PIOASMEmit_irq + 12,
        .opcodes = fun_data_rp2_PIOASMEmit_irq + 12,
    },
    #endif
    #endif
};
#else
#define proto_fun_rp2_PIOASMEmit_irq fun_data_rp2_PIOASMEmit_irq[0]
#endif

// child of rp2_PIOASMEmit
// frozen bytecode for file rp2.py, scope rp2_PIOASMEmit_set
static const byte fun_data_rp2_PIOASMEmit_set[24] = {
    0x3b,0x0c, // prelude
    0x2f,0x5c,0x66,0x65, // names: set, self, dest, data
    0x80,0xb0, // code info
    0xb0, // LOAD_FAST 0
    0x14,0x25, // LOAD_METHOD 'word'
    0x22,0x83,0xc0,0x00, // LOAD_CONST_SMALL_INT 57344
    0xb1, // LOAD_FAST 1
    0x85, // LOAD_CONST_SMALL_INT 5
    0xf0, // BINARY_OP 25 __lshift__
    0xed, // BINARY_OP 22 __or__
    0xb2, // LOAD_FAST 2
    0xed, // BINARY_OP 22 __or__
    0x36,0x01, // CALL_METHOD 1
    0x63, // RETURN_VALUE
};
#if MICROPY_PERSISTENT_CODE_SAVE
static const mp_raw_code_truncated_t proto_fun_rp2_PIOASMEmit_set = {
    .proto_fun_indicator[0] = MP_PROTO_FUN_INDICATOR_RAW_CODE_0,
    .proto_fun_indicator[1] = MP_PROTO_FUN_INDICATOR_RAW_CODE_1,
    .kind = MP_CODE_BYTECODE,
    .is_generator = 0,
    .fun_data = fun_data_rp2_PIOASMEmit_set,
    .children = NULL,
    #if MICROPY_PERSISTENT_CODE_SAVE
    .fun_data_len = 24,
    .n_children = 0,
    #if MICROPY_EMIT_MACHINE_CODE
    .prelude_offset = 0,
    #endif
    #if MICROPY_PY_SYS_SETTRACE
    .line_of_definition = 0,
    .prelude = {
        .n_state = 8,
        .n_exc_stack = 0,
        .scope_flags = 0,
        .n_pos_args = 3,
        .n_kwonly_args = 0,
        .n_def_pos_args = 0,
        .qstr_block_name_idx = 47,
        .line_info = fun_data_rp2_PIOASMEmit_set + 6,
        .line_info_top = fun_data_rp2_PIOASMEmit_set + 8,
        .opcodes = fun_data_rp2_PIOASMEmit_set + 8,
    },
    #endif
    #endif
};
#else
#define proto_fun_rp2_PIOASMEmit_set fun_data_rp2_PIOASMEmit_set[0]
#endif

static const mp_raw_code_t *const children_rp2_PIOASMEmit[] = {
    (const mp_raw_code_t *)&proto_fun_rp2_PIOASMEmit___init__,
    (const mp_raw_code_t *)&proto_fun_rp2_PIOASMEmit_start_pass,
    (const mp_raw_code_t *)&proto_fun_rp2_PIOASMEmit___getitem__,
    (const mp_raw_code_t *)&proto_fun_rp2_PIOASMEmit_delay,
    (const mp_raw_code_t *)&proto_fun_rp2_PIOASMEmit_side,
    (const mp_raw_code_t *)&proto_fun_rp2_PIOASMEmit_wrap_target,
    (const mp_raw_code_t *)&proto_fun_rp2_PIOASMEmit_wrap,
    (const mp_raw_code_t *)&proto_fun_rp2_PIOASMEmit_label,
    (const mp_raw_code_t *)&proto_fun_rp2_PIOASMEmit_word,
    (const mp_raw_code_t *)&proto_fun_rp2_PIOASMEmit_nop,
    (const mp_raw_code_t *)&proto_fun_rp2_PIOASMEmit_jmp,
    (const mp_raw_code_t *)&proto_fun_rp2_PIOASMEmit_wait,
    (const mp_raw_code_t *)&proto_fun_rp2_PIOASMEmit_in_,
    (const mp_raw_code_t *)&proto_fun_rp2_PIOASMEmit_out,
    (const mp_raw_code_t *)&proto_fun_rp2_PIOASMEmit_push,
    (const mp_raw_code_t *)&proto_fun_rp2_PIOASMEmit_pull,
    (const mp_raw_code_t *)&proto_fun_rp2_PIOASMEmit_mov,
    (const mp_raw_code_t *)&proto_fun_rp2_PIOASMEmit_irq,
    (const mp_raw_code_t *)&proto_fun_rp2_PIOASMEmit_set,
};

static const mp_raw_code_truncated_t proto_fun_rp2_PIOASMEmit = {
    .proto_fun_indicator[0] = MP_PROTO_FUN_INDICATOR_RAW_CODE_0,
    .proto_fun_indicator[1] = MP_PROTO_FUN_INDICATOR_RAW_CODE_1,
    .kind = MP_CODE_BYTECODE,
    .is_generator = 0,
    .fun_data = fun_data_rp2_PIOASMEmit,
    .children = (void *)&children_rp2_PIOASMEmit,
    #if MICROPY_PERSISTENT_CODE_SAVE
    .fun_data_len = 191,
    .n_children = 19,
    #if MICROPY_EMIT_MACHINE_CODE
    .prelude_offset = 0,
    #endif
    #if MICROPY_PY_SYS_SETTRACE
    .line_of_definition = 0,
    .prelude = {
        .n_state = 4,
        .n_exc_stack = 0,
        .scope_flags = 0,
        .n_pos_args = 0,
        .n_kwonly_args = 0,
        .n_def_pos_args = 0,
        .qstr_block_name_idx = 7,
        .line_info = fun_data_rp2_PIOASMEmit + 3,
        .line_info_top = fun_data_rp2_PIOASMEmit + 40,
        .opcodes = fun_data_rp2_PIOASMEmit + 40,
    },
    #endif
    #endif
};

// child of rp2__lt_module_gt_
// frozen bytecode for file rp2.py, scope rp2__lt_lambda_gt_
static const byte fun_data_rp2__lt_lambda_gt_[10] = {
    0x11,0x08, // prelude
    0x3a,0x0a, // names: <lambda>, x
    0x80,0xc4, // code info
    0xb0, // LOAD_FAST 0
    0x88, // LOAD_CONST_SMALL_INT 8
    0xed, // BINARY_OP 22 __or__
    0x63, // RETURN_VALUE
};
#if MICROPY_PERSISTENT_CODE_SAVE
static const mp_raw_code_truncated_t proto_fun_rp2__lt_lambda_gt_ = {
    .proto_fun_indicator[0] = MP_PROTO_FUN_INDICATOR_RAW_CODE_0,
    .proto_fun_indicator[1] = MP_PROTO_FUN_INDICATOR_RAW_CODE_1,
    .kind = MP_CODE_BYTECODE,
    .is_generator = 0,
    .fun_data = fun_data_rp2__lt_lambda_gt_,
    .children = NULL,
    #if MICROPY_PERSISTENT_CODE_SAVE
    .fun_data_len = 10,
    .n_children = 0,
    #if MICROPY_EMIT_MACHINE_CODE
    .prelude_offset = 0,
    #endif
    #if MICROPY_PY_SYS_SETTRACE
    .line_of_definition = 0,
    .prelude = {
        .n_state = 3,
        .n_exc_stack = 0,
        .scope_flags = 0,
        .n_pos_args = 1,
        .n_kwonly_args = 0,
        .n_def_pos_args = 0,
        .qstr_block_name_idx = 58,
        .line_info = fun_data_rp2__lt_lambda_gt_ + 4,
        .line_info_top = fun_data_rp2__lt_lambda_gt_ + 6,
        .opcodes = fun_data_rp2__lt_lambda_gt_ + 6,
    },
    #endif
    #endif
};
#else
#define proto_fun_rp2__lt_lambda_gt_ fun_data_rp2__lt_lambda_gt_[0]
#endif

// child of rp2__lt_module_gt_
// frozen bytecode for file rp2.py, scope rp2__lt_lambda_gt_2
static const byte fun_data_rp2__lt_lambda_gt_2[10] = {
    0x11,0x08, // prelude
    0x3a,0x0a, // names: <lambda>, x
    0x80,0xc5, // code info
    0xb0, // LOAD_FAST 0
    0x90, // LOAD_CONST_SMALL_INT 16
    0xed, // BINARY_OP 22 __or__
    0x63, // RETURN_VALUE
};
#if MICROPY_PERSISTENT_CODE_SAVE
static const mp_raw_code_truncated_t proto_fun_rp2__lt_lambda_gt_2 = {
    .proto_fun_indicator[0] = MP_PROTO_FUN_INDICATOR_RAW_CODE_0,
    .proto_fun_indicator[1] = MP_PROTO_FUN_INDICATOR_RAW_CODE_1,
    .kind = MP_CODE_BYTECODE,
    .is_generator = 0,
    .fun_data = fun_data_rp2__lt_lambda_gt_2,
    .children = NULL,
    #if MICROPY_PERSISTENT_CODE_SAVE
    .fun_data_len = 10,
    .n_children = 0,
    #if MICROPY_EMIT_MACHINE_CODE
    .prelude_offset = 0,
    #endif
    #if MICROPY_PY_SYS_SETTRACE
    .line_of_definition = 0,
    .prelude = {
        .n_state = 3,
        .n_exc_stack = 0,
        .scope_flags = 0,
        .n_pos_args = 1,
        .n_kwonly_args = 0,
        .n_def_pos_args = 0,
        .qstr_block_name_idx = 58,
        .line_info = fun_data_rp2__lt_lambda_gt_2 + 4,
        .line_info_top = fun_data_rp2__lt_lambda_gt_2 + 6,
        .opcodes = fun_data_rp2__lt_lambda_gt_2 + 6,
    },
    #endif
    #endif
};
#else
#define proto_fun_rp2__lt_lambda_gt_2 fun_data_rp2__lt_lambda_gt_2[0]
#endif

// child of rp2__lt_module_gt_
// frozen bytecode for file rp2.py, scope rp2__lt_lambda_gt_3
static const byte fun_data_rp2__lt_lambda_gt_3[10] = {
    0x11,0x08, // prelude
    0x3a,0x0a, // names: <lambda>, x
    0x80,0xd7, // code info
    0xb0, // LOAD_FAST 0
    0x90, // LOAD_CONST_SMALL_INT 16
    0xed, // BINARY_OP 22 __or__
    0x63, // RETURN_VALUE
};
#if MICROPY_PERSISTENT_CODE_SAVE
static const mp_raw_code_truncated_t proto_fun_rp2__lt_lambda_gt_3 = {
    .proto_fun_indicator[0] = MP_PROTO_FUN_INDICATOR_RAW_CODE_0,
    .proto_fun_indicator[1] = MP_PROTO_FUN_INDICATOR_RAW_CODE_1,
    .kind = MP_CODE_BYTECODE,
    .is_generator = 0,
    .fun_data = fun_data_rp2__lt_lambda_gt_3,
    .children = NULL,
    #if MICROPY_PERSISTENT_CODE_SAVE
    .fun_data_len = 10,
    .n_children = 0,
    #if MICROPY_EMIT_MACHINE_CODE
    .prelude_offset = 0,
    #endif
    #if MICROPY_PY_SYS_SETTRACE
    .line_of_definition = 0,
    .prelude = {
        .n_state = 3,
        .n_exc_stack = 0,
        .scope_flags = 0,
        .n_pos_args = 1,
        .n_kwonly_args = 0,
        .n_def_pos_args = 0,
        .qstr_block_name_idx = 58,
        .line_info = fun_data_rp2__lt_lambda_gt_3 + 4,
        .line_info_top = fun_data_rp2__lt_lambda_gt_3 + 6,
        .opcodes = fun_data_rp2__lt_lambda_gt_3 + 6,
    },
    #endif
    #endif
};
#else
#define proto_fun_rp2__lt_lambda_gt_3 fun_data_rp2__lt_lambda_gt_3[0]
#endif

// child of rp2__lt_module_gt_
// frozen bytecode for file rp2.py, scope rp2_asm_pio
static const byte fun_data_rp2_asm_pio[28] = {
    0xb0,0x80,0x40,0x0d, // prelude
    0x3b, // names: asm_pio
    0x80,0xeb,0x4a,0x85,0x22,0x02, // code info
    0x12,0x07, // LOAD_GLOBAL 'PIOASMEmit'
    0x53, // LOAD_NULL
    0xb0, // LOAD_FAST 0
    0x80, // LOAD_CONST_SMALL_INT 0
    0x35,0x82,0x00, // CALL_FUNCTION_VAR_KW 256
    0x27,0x02, // STORE_DEREF 2
    0xb2, // LOAD_FAST 2
    0x20,0x00,0x01, // MAKE_CLOSURE 0
    0xc1, // STORE_FAST 1
    0xb1, // LOAD_FAST 1
    0x63, // RETURN_VALUE
};
// child of rp2_asm_pio
// frozen bytecode for file rp2.py, scope rp2_asm_pio_dec
static const byte fun_data_rp2_asm_pio_dec[218] = {
    0x32,0x3c, // prelude
    0x51,0x02,0x69, // names: dec, *, f
    0x80,0xee,0x40,0x23,0x28,0x28,0x28,0x28,0x28,0x28,0x28,0x28,0x28,0x28,0x28,0x28,0x28,0x48,0x28,0x28,0x49,0x28,0x44,0x28,0x44,0x28,0x49, // code info
    0x12,0x56, // LOAD_GLOBAL '_pio_funcs'
    0xc2, // STORE_FAST 2
    0x25,0x00, // LOAD_DEREF 0
    0x13,0x22, // LOAD_ATTR 'wrap_target'
    0xb2, // LOAD_FAST 2
    0x10,0x22, // LOAD_CONST_STRING 'wrap_target'
    0x56, // STORE_SUBSCR
    0x25,0x00, // LOAD_DEREF 0
    0x13,0x23, // LOAD_ATTR 'wrap'
    0xb2, // LOAD_FAST 2
    0x10,0x23, // LOAD_CONST_STRING 'wrap'
    0x56, // STORE_SUBSCR
    0x25,0x00, // LOAD_DEREF 0
    0x13,0x24, // LOAD_ATTR 'label'
    0xb2, // LOAD_FAST 2
    0x10,0x24, // LOAD_CONST_STRING 'label'
    0x56, // STORE_SUBSCR
    0x25,0x00, // LOAD_DEREF 0
    0x13,0x25, // LOAD_ATTR 'word'
    0xb2, // LOAD_FAST 2
    0x10,0x25, // LOAD_CONST_STRING 'word'
    0x56, // STORE_SUBSCR
    0x25,0x00, // LOAD_DEREF 0
    0x13,0x26, // LOAD_ATTR 'nop'
    0xb2, // LOAD_FAST 2
    0x10,0x26, // LOAD_CONST_STRING 'nop'
    0x56, // STORE_SUBSCR
    0x25,0x00, // LOAD_DEREF 0
    0x13,0x27, // LOAD_ATTR 'jmp'
    0xb2, // LOAD_FAST 2
    0x10,0x27, // LOAD_CONST_STRING 'jmp'
    0x56, // STORE_SUBSCR
    0x25,0x00, // LOAD_DEREF 0
    0x13,0x28, // LOAD_ATTR 'wait'
    0xb2, // LOAD_FAST 2
    0x10,0x28, // LOAD_CONST_STRING 'wait'
    0x56, // STORE_SUBSCR
    0x25,0x00, // LOAD_DEREF 0
    0x13,0x29, // LOAD_ATTR 'in_'
    0xb2, // LOAD_FAST 2
    0x10,0x29, // LOAD_CONST_STRING 'in_'
    0x56, // STORE_SUBSCR
    0x25,0x00, // LOAD_DEREF 0
    0x13,0x2a, // LOAD_ATTR 'out'
    0xb2, // LOAD_FAST 2
    0x10,0x2a, // LOAD_CONST_STRING 'out'
    0x56, // STORE_SUBSCR
    0x25,0x00, // LOAD_DEREF 0
    0x13,0x2b, // LOAD_ATTR 'push'
    0xb2, // LOAD_FAST 2
    0x10,0x2b, // LOAD_CONST_STRING 'push'
    0x56, // STORE_SUBSCR
    0x25,0x00, // LOAD_DEREF 0
    0x13,0x2c, // LOAD_ATTR 'pull'
    0xb2, // LOAD_FAST 2
    0x10,0x2c, // LOAD_CONST_STRING 'pull'
    0x56, // STORE_SUBSCR
    0x25,0x00, // LOAD_DEREF 0
    0x13,0x2d, // LOAD_ATTR 'mov'
    0xb2, // LOAD_FAST 2
    0x10,0x2d, // LOAD_CONST_STRING 'mov'
    0x56, // STORE_SUBSCR
    0x25,0x00, // LOAD_DEREF 0
    0x13,0x2e, // LOAD_ATTR 'irq'
    0xb2, // LOAD_FAST 2
    0x10,0x2e, // LOAD_CONST_STRING 'irq'
    0x56, // STORE_SUBSCR
    0x25,0x00, // LOAD_DEREF 0
    0x13,0x2f, // LOAD_ATTR 'set'
    0xb2, // LOAD_FAST 2
    0x10,0x2f, // LOAD_CONST_STRING 'set'
    0x56, // STORE_SUBSCR
    0xb1, // LOAD_FAST 1
    0x13,0x52, // LOAD_ATTR '__globals__'
    0x14,0x53, // LOAD_METHOD 'copy'
    0x36,0x00, // CALL_METHOD 0
    0xc3, // STORE_FAST 3
    0xb1, // LOAD_FAST 1
    0x13,0x52, // LOAD_ATTR '__globals__'
    0x14,0x20, // LOAD_METHOD 'clear'
    0x36,0x00, // CALL_METHOD 0
    0x59, // POP_TOP
    0xb1, // LOAD_FAST 1
    0x13,0x52, // LOAD_ATTR '__globals__'
    0x14,0x54, // LOAD_METHOD 'update'
    0xb2, // LOAD_FAST 2
    0x36,0x01, // CALL_METHOD 1
    0x59, // POP_TOP
    0x25,0x00, // LOAD_DEREF 0
    0x14,0x49, // LOAD_METHOD 'start_pass'
    0x80, // LOAD_CONST_SMALL_INT 0
    0x36,0x01, // CALL_METHOD 1
    0x59, // POP_TOP
    0xb1, // LOAD_FAST 1
    0x34,0x00, // CALL_FUNCTION 0
    0x59, // POP_TOP
    0x25,0x00, // LOAD_DEREF 0
    0x14,0x49, // LOAD_METHOD 'start_pass'
    0x81, // LOAD_CONST_SMALL_INT 1
    0x36,0x01, // CALL_METHOD 1
    0x59, // POP_TOP
    0xb1, // LOAD_FAST 1
    0x34,0x00, // CALL_FUNCTION 0
    0x59, // POP_TOP
    0xb1, // LOAD_FAST 1
    0x13,0x52, // LOAD_ATTR '__globals__'
    0x14,0x20, // LOAD_METHOD 'clear'
    0x36,0x00, // CALL_METHOD 0
    0x59, // POP_TOP
    0xb1, // LOAD_FAST 1
    0x13,0x52, // LOAD_ATTR '__globals__'
    0x14,0x54, // LOAD_METHOD 'update'
    0xb3, // LOAD_FAST 3
    0x36,0x01, // CALL_METHOD 1
    0x59, // POP_TOP
    0x25,0x00, // LOAD_DEREF 0
    0x13,0x43, // LOAD_ATTR 'prog'
    0x63, // RETURN_VALUE
};
#if MICROPY_PERSISTENT_CODE_SAVE
static const mp_raw_code_truncated_t proto_fun_rp2_asm_pio_dec = {
    .proto_fun_indicator[0] = MP_PROTO_FUN_INDICATOR_RAW_CODE_0,
    .proto_fun_indicator[1] = MP_PROTO_FUN_INDICATOR_RAW_CODE_1,
    .kind = MP_CODE_BYTECODE,
    .is_generator = 0,
    .fun_data = fun_data_rp2_asm_pio_dec,
    .children = NULL,
    #if MICROPY_PERSISTENT_CODE_SAVE
    .fun_data_len = 218,
    .n_children = 0,
    #if MICROPY_EMIT_MACHINE_CODE
    .prelude_offset = 0,
    #endif
    #if MICROPY_PY_SYS_SETTRACE
    .line_of_definition = 0,
    .prelude = {
        .n_state = 7,
        .n_exc_stack = 0,
        .scope_flags = 0,
        .n_pos_args = 2,
        .n_kwonly_args = 0,
        .n_def_pos_args = 0,
        .qstr_block_name_idx = 81,
        .line_info = fun_data_rp2_asm_pio_dec + 5,
        .line_info_top = fun_data_rp2_asm_pio_dec + 32,
        .opcodes = fun_data_rp2_asm_pio_dec + 32,
    },
    #endif
    #endif
};
#else
#define proto_fun_rp2_asm_pio_dec fun_data_rp2_asm_pio_dec[0]
#endif

static const mp_raw_code_t *const children_rp2_asm_pio[] = {
    (const mp_raw_code_t *)&proto_fun_rp2_asm_pio_dec,
};

static const mp_raw_code_truncated_t proto_fun_rp2_asm_pio = {
    .proto_fun_indicator[0] = MP_PROTO_FUN_INDICATOR_RAW_CODE_0,
    .proto_fun_indicator[1] = MP_PROTO_FUN_INDICATOR_RAW_CODE_1,
    .kind = MP_CODE_BYTECODE,
    .is_generator = 0,
    .fun_data = fun_data_rp2_asm_pio,
    .children = (void *)&children_rp2_asm_pio,
    #if MICROPY_PERSISTENT_CODE_SAVE
    .fun_data_len = 28,
    .n_children = 1,
    #if MICROPY_EMIT_MACHINE_CODE
    .prelude_offset = 0,
    #endif
    #if MICROPY_PY_SYS_SETTRACE
    .line_of_definition = 0,
    .prelude = {
        .n_state = 7,
        .n_exc_stack = 0,
        .scope_flags = 2,
        .n_pos_args = 0,
        .n_kwonly_args = 0,
        .n_def_pos_args = 0,
        .qstr_block_name_idx = 59,
        .line_info = fun_data_rp2_asm_pio + 5,
        .line_info_top = fun_data_rp2_asm_pio + 10,
        .opcodes = fun_data_rp2_asm_pio + 11,
    },
    #endif
    #endif
};

// child of rp2__lt_module_gt_
// frozen bytecode for file rp2.py, scope rp2_asm_pio_encode
static const byte fun_data_rp2_asm_pio_encode[177] = {
    0xbb,0x01,0x36, // prelude
    0x3c,0x5a,0x3d,0x3e, // names: asm_pio_encode, instr, sideset_count, sideset_opt
    0x90,0x14,0x25,0x24,0x26,0x2c,0x24,0x24,0x44,0x23,0x27,0x47,0x27,0x27,0x27,0x27,0x27,0x27,0x27,0x47,0x47,0x2d,0x27, // code info
    0x12,0x07, // LOAD_GLOBAL 'PIOASMEmit'
    0x34,0x00, // CALL_FUNCTION 0
    0xc3, // STORE_FAST 3
    0xb1, // LOAD_FAST 1
    0xb3, // LOAD_FAST 3
    0x18,0x3d, // STORE_ATTR 'sideset_count'
    0xb2, // LOAD_FAST 2
    0x80, // LOAD_CONST_SMALL_INT 0
    0xdc, // BINARY_OP 5 __ne__
    0xb3, // LOAD_FAST 3
    0x18,0x3e, // STORE_ATTR 'sideset_opt'
    0x9f, // LOAD_CONST_SMALL_INT 31
    0xb3, // LOAD_FAST 3
    0x13,0x3d, // LOAD_ATTR 'sideset_count'
    0xb3, // LOAD_FAST 3
    0x13,0x3e, // LOAD_ATTR 'sideset_opt'
    0xf2, // BINARY_OP 27 __add__
    0xf1, // BINARY_OP 26 __rshift__
    0xb3, // LOAD_FAST 3
    0x18,0x3f, // STORE_ATTR 'delay_max'
    0x81, // LOAD_CONST_SMALL_INT 1
    0xb3, // LOAD_FAST 3
    0x18,0x40, // STORE_ATTR 'pass_'
    0x80, // LOAD_CONST_SMALL_INT 0
    0xb3, // LOAD_FAST 3
    0x18,0x41, // STORE_ATTR 'num_instr'
    0x80, // LOAD_CONST_SMALL_INT 0
    0xb3, // LOAD_FAST 3
    0x18,0x42, // STORE_ATTR 'num_sideset'
    0x12,0x56, // LOAD_GLOBAL '_pio_funcs'
    0xc4, // STORE_FAST 4
    0xb3, // LOAD_FAST 3
    0x13,0x25, // LOAD_ATTR 'word'
    0xb4, // LOAD_FAST 4
    0x10,0x25, // LOAD_CONST_STRING 'word'
    0x56, // STORE_SUBSCR
    0xb3, // LOAD_FAST 3
    0x13,0x26, // LOAD_ATTR 'nop'
    0xb4, // LOAD_FAST 4
    0x10,0x26, // LOAD_CONST_STRING 'nop'
    0x56, // STORE_SUBSCR
    0xb3, // LOAD_FAST 3
    0x13,0x28, // LOAD_ATTR 'wait'
    0xb4, // LOAD_FAST 4
    0x10,0x28, // LOAD_CONST_STRING 'wait'
    0x56, // STORE_SUBSCR
    0xb3, // LOAD_FAST 3
    0x13,0x29, // LOAD_ATTR 'in_'
    0xb4, // LOAD_FAST 4
    0x10,0x29, // LOAD_CONST_STRING 'in_'
    0x56, // STORE_SUBSCR
    0xb3, // LOAD_FAST 3
    0x13,0x2a, // LOAD_ATTR 'out'
    0xb4, // LOAD_FAST 4
    0x10,0x2a, // LOAD_CONST_STRING 'out'
    0x56, // STORE_SUBSCR
    0xb3, // LOAD_FAST 3
    0x13,0x2b, // LOAD_ATTR 'push'
    0xb4, // LOAD_FAST 4
    0x10,0x2b, // LOAD_CONST_STRING 'push'
    0x56, // STORE_SUBSCR
    0xb3, // LOAD_FAST 3
    0x13,0x2c, // LOAD_ATTR 'pull'
    0xb4, // LOAD_FAST 4
    0x10,0x2c, // LOAD_CONST_STRING 'pull'
    0x56, // STORE_SUBSCR
    0xb3, // LOAD_FAST 3
    0x13,0x2d, // LOAD_ATTR 'mov'
    0xb4, // LOAD_FAST 4
    0x10,0x2d, // LOAD_CONST_STRING 'mov'
    0x56, // STORE_SUBSCR
    0xb3, // LOAD_FAST 3
    0x13,0x2e, // LOAD_ATTR 'irq'
    0xb4, // LOAD_FAST 4
    0x10,0x2e, // LOAD_CONST_STRING 'irq'
    0x56, // STORE_SUBSCR
    0xb3, // LOAD_FAST 3
    0x13,0x2f, // LOAD_ATTR 'set'
    0xb4, // LOAD_FAST 4
    0x10,0x2f, // LOAD_CONST_STRING 'set'
    0x56, // STORE_SUBSCR
    0x12,0x12, // LOAD_GLOBAL 'exec'
    0xb0, // LOAD_FAST 0
    0xb4, // LOAD_FAST 4
    0x34,0x02, // CALL_FUNCTION 2
    0x59, // POP_TOP
    0x12,0x5b, // LOAD_GLOBAL 'len'
    0xb3, // LOAD_FAST 3
    0x13,0x43, // LOAD_ATTR 'prog'
    0x80, // LOAD_CONST_SMALL_INT 0
    0x55, // LOAD_SUBSCR
    0x34,0x01, // CALL_FUNCTION 1
    0x81, // LOAD_CONST_SMALL_INT 1
    0xdc, // BINARY_OP 5 __ne__
    0x44,0x47, // POP_JUMP_IF_FALSE 7
    0x12,0x06, // LOAD_GLOBAL 'PIOASMError'
    0x23,0x00, // LOAD_CONST_OBJ 0
    0x34,0x01, // CALL_FUNCTION 1
    0x65, // RAISE_OBJ
    0xb3, // LOAD_FAST 3
    0x13,0x43, // LOAD_ATTR 'prog'
    0x80, // LOAD_CONST_SMALL_INT 0
    0x55, // LOAD_SUBSCR
    0x80, // LOAD_CONST_SMALL_INT 0
    0x55, // LOAD_SUBSCR
    0x63, // RETURN_VALUE
};
#if MICROPY_PERSISTENT_CODE_SAVE
static const mp_raw_code_truncated_t proto_fun_rp2_asm_pio_encode = {
    .proto_fun_indicator[0] = MP_PROTO_FUN_INDICATOR_RAW_CODE_0,
    .proto_fun_indicator[1] = MP_PROTO_FUN_INDICATOR_RAW_CODE_1,
    .kind = MP_CODE_BYTECODE,
    .is_generator = 0,
    .fun_data = fun_data_rp2_asm_pio_encode,
    .children = NULL,
    #if MICROPY_PERSISTENT_CODE_SAVE
    .fun_data_len = 177,
    .n_children = 0,
    #if MICROPY_EMIT_MACHINE_CODE
    .prelude_offset = 0,
    #endif
    #if MICROPY_PY_SYS_SETTRACE
    .line_of_definition = 0,
    .prelude = {
        .n_state = 8,
        .n_exc_stack = 0,
        .scope_flags = 0,
        .n_pos_args = 3,
        .n_kwonly_args = 0,
        .n_def_pos_args = 1,
        .qstr_block_name_idx = 60,
        .line_info = fun_data_rp2_asm_pio_encode + 7,
        .line_info_top = fun_data_rp2_asm_pio_encode + 30,
        .opcodes = fun_data_rp2_asm_pio_encode + 30,
    },
    #endif
    #endif
};
#else
#define proto_fun_rp2_asm_pio_encode fun_data_rp2_asm_pio_encode[0]
#endif

static const mp_raw_code_t *const children_rp2__lt_module_gt_[] = {
    (const mp_raw_code_t *)&proto_fun_rp2_PIOASMError,
    (const mp_raw_code_t *)&proto_fun_rp2_PIOASMEmit,
    (const mp_raw_code_t *)&proto_fun_rp2__lt_lambda_gt_,
    (const mp_raw_code_t *)&proto_fun_rp2__lt_lambda_gt_2,
    (const mp_raw_code_t *)&proto_fun_rp2__lt_lambda_gt_3,
    (const mp_raw_code_t *)&proto_fun_rp2_asm_pio,
    (const mp_raw_code_t *)&proto_fun_rp2_asm_pio_encode,
};

static const mp_raw_code_truncated_t proto_fun_rp2__lt_module_gt_ = {
    .proto_fun_indicator[0] = MP_PROTO_FUN_INDICATOR_RAW_CODE_0,
    .proto_fun_indicator[1] = MP_PROTO_FUN_INDICATOR_RAW_CODE_1,
    .kind = MP_CODE_BYTECODE,
    .is_generator = 0,
    .fun_data = fun_data_rp2__lt_module_gt_,
    .children = (void *)&children_rp2__lt_module_gt_,
    #if MICROPY_PERSISTENT_CODE_SAVE
    .fun_data_len = 284,
    .n_children = 7,
    #if MICROPY_EMIT_MACHINE_CODE
    .prelude_offset = 0,
    #endif
    #if MICROPY_PY_SYS_SETTRACE
    .line_of_definition = 0,
    .prelude = {
        .n_state = 4,
        .n_exc_stack = 0,
        .scope_flags = 0,
        .n_pos_args = 0,
        .n_kwonly_args = 0,
        .n_def_pos_args = 0,
        .qstr_block_name_idx = 1,
        .line_info = fun_data_rp2__lt_module_gt_ + 3,
        .line_info_top = fun_data_rp2__lt_module_gt_ + 57,
        .opcodes = fun_data_rp2__lt_module_gt_ + 57,
    },
    #endif
    #endif
};

static const qstr_short_t const_qstr_table_data_rp2[106] = {
    MP_QSTR_rp2_dot_py,
    MP_QSTR__lt_module_gt_,
    MP_QSTR__star_,
    MP_QSTR__rp2,
    MP_QSTR_const,
    MP_QSTR_micropython,
    MP_QSTR_PIOASMError,
    MP_QSTR_PIOASMEmit,
    MP_QSTR_gpio,
    MP_QSTR_pins,
    MP_QSTR_x,
    MP_QSTR_y,
    MP_QSTR_null,
    MP_QSTR_pindirs,
    MP_QSTR_pc,
    MP_QSTR_status,
    MP_QSTR_isr,
    MP_QSTR_osr,
    MP_QSTR_exec,
    MP_QSTR_invert,
    MP_QSTR_reverse,
    MP_QSTR_not_x,
    MP_QSTR_x_dec,
    MP_QSTR_not_y,
    MP_QSTR_y_dec,
    MP_QSTR_x_not_y,
    MP_QSTR_pin,
    MP_QSTR_not_osre,
    MP_QSTR_noblock,
    MP_QSTR_block,
    MP_QSTR_iffull,
    MP_QSTR_ifempty,
    MP_QSTR_clear,
    MP_QSTR_rel,
    MP_QSTR_wrap_target,
    MP_QSTR_wrap,
    MP_QSTR_label,
    MP_QSTR_word,
    MP_QSTR_nop,
    MP_QSTR_jmp,
    MP_QSTR_wait,
    MP_QSTR_in_,
    MP_QSTR_out,
    MP_QSTR_push,
    MP_QSTR_pull,
    MP_QSTR_mov,
    MP_QSTR_irq,
    MP_QSTR_set,
    MP_QSTR_out_init,
    MP_QSTR_set_init,
    MP_QSTR_sideset_init,
    MP_QSTR_in_shiftdir,
    MP_QSTR_out_shiftdir,
    MP_QSTR_autopush,
    MP_QSTR_autopull,
    MP_QSTR_push_thresh,
    MP_QSTR_pull_thresh,
    MP_QSTR_fifo_join,
    MP_QSTR__lt_lambda_gt_,
    MP_QSTR_asm_pio,
    MP_QSTR_asm_pio_encode,
    MP_QSTR_sideset_count,
    MP_QSTR_sideset_opt,
    MP_QSTR_delay_max,
    MP_QSTR_pass_,
    MP_QSTR_num_instr,
    MP_QSTR_num_sideset,
    MP_QSTR_prog,
    MP_QSTR___init__,
    MP_QSTR_array,
    MP_QSTR_labels,
    MP_QSTR_H,
    MP_QSTR_wrap_used,
    MP_QSTR_start_pass,
    MP_QSTR___getitem__,
    MP_QSTR_delay,
    MP_QSTR_side,
    MP_QSTR_no_space_sideset,
    MP_QSTR_AssertionError,
    MP_QSTR_format,
    MP_QSTR_append,
    MP_QSTR_dec,
    MP_QSTR___globals__,
    MP_QSTR_copy,
    MP_QSTR_update,
    MP_QSTR_Exception,
    MP_QSTR__pio_funcs,
    MP_QSTR___name__,
    MP_QSTR___module__,
    MP_QSTR___qualname__,
    MP_QSTR_instr,
    MP_QSTR_len,
    MP_QSTR_self,
    MP_QSTR_isinstance,
    MP_QSTR_int,
    MP_QSTR_key,
    MP_QSTR_value,
    MP_QSTR_cond,
    MP_QSTR_polarity,
    MP_QSTR_src,
    MP_QSTR_index,
    MP_QSTR_data,
    MP_QSTR_dest,
    MP_QSTR_value2,
    MP_QSTR_mod,
    MP_QSTR_f,
};

// constants
static const mp_obj_str_t const_obj_rp2_0 = {{&mp_type_str}, 13, 31, (const byte*)"\x65\x78\x70\x65\x63\x74\x69\x6e\x67\x20\x65\x78\x61\x63\x74\x6c\x79\x20\x31\x20\x69\x6e\x73\x74\x72\x75\x63\x74\x69\x6f\x6e"};
static const mp_obj_int_t const_obj_rp2_1 = {{&mp_type_int}, {.neg=0, .fixed_dig=1, .alloc=2, .len=2, .dig=(uint16_t*)(const uint16_t[]){0x0,0x4000}}};

// constant table
static const mp_rom_obj_t const_obj_table_data_rp2[7] = {
    MP_ROM_PTR(&const_obj_rp2_0),
    MP_ROM_PTR(&const_obj_rp2_1),
    MP_ROM_QSTR(MP_QSTR_delay_space_too_space_large),
    MP_ROM_QSTR(MP_QSTR_sideset_space_too_space_large),
    MP_ROM_QSTR(MP_QSTR_duplicate_space_label_space__brace_open__brace_close_),
    MP_ROM_QSTR(MP_QSTR_unknown_space_label_space__brace_open__brace_close_),
    MP_ROM_QSTR(MP_QSTR_invalid_space_bit_space_count_space__brace_open__brace_close_),
};

static const mp_frozen_module_t frozen_module_rp2 = {
    .constants = {
        .qstr_table = (qstr_short_t *)&const_qstr_table_data_rp2,
        .obj_table = (mp_obj_t *)&const_obj_table_data_rp2,
    },
    .proto_fun = &proto_fun_rp2__lt_module_gt_,
};

////////////////////////////////////////////////////////////////////////////////
// frozen module asyncio___init__
// - original source file: /home/atul/micropython/ports/rp2/build-ATRIVATECH_PICUNO/frozen_mpy/asyncio/__init__.mpy
// - frozen file name: asyncio/__init__.py
// - .mpy header: 4d:06:00:1f

// frozen bytecode for file asyncio/__init__.py, scope asyncio___init____lt_module_gt_
static const byte fun_data_asyncio___init____lt_module_gt_[75] = {
    0x10,0x02, // prelude
    0x01, // names: <module>
     // code info
    0x81, // LOAD_CONST_SMALL_INT 1
    0x10,0x02, // LOAD_CONST_STRING '*'
    0x2a,0x01, // BUILD_TUPLE 1
    0x1b,0x03, // IMPORT_NAME 'core'
    0x69, // IMPORT_STAR
    0x23,0x00, // LOAD_CONST_OBJ 0
    0x16,0x0e, // STORE_NAME '__version__'
    0x2c,0x0a, // BUILD_MAP 10
    0x10,0x04, // LOAD_CONST_STRING 'funcs'
    0x10,0x05, // LOAD_CONST_STRING 'wait_for'
    0x62, // STORE_MAP
    0x10,0x04, // LOAD_CONST_STRING 'funcs'
    0x23,0x01, // LOAD_CONST_OBJ 1
    0x62, // STORE_MAP
    0x10,0x04, // LOAD_CONST_STRING 'funcs'
    0x10,0x06, // LOAD_CONST_STRING 'gather'
    0x62, // STORE_MAP
    0x10,0x07, // LOAD_CONST_STRING 'event'
    0x10,0x08, // LOAD_CONST_STRING 'Event'
    0x62, // STORE_MAP
    0x10,0x07, // LOAD_CONST_STRING 'event'
    0x23,0x02, // LOAD_CONST_OBJ 2
    0x62, // STORE_MAP
    0x10,0x09, // LOAD_CONST_STRING 'lock'
    0x10,0x0a, // LOAD_CONST_STRING 'Lock'
    0x62, // STORE_MAP
    0x10,0x0b, // LOAD_CONST_STRING 'stream'
    0x23,0x03, // LOAD_CONST_OBJ 3
    0x62, // STORE_MAP
    0x10,0x0b, // LOAD_CONST_STRING 'stream'
    0x23,0x04, // LOAD_CONST_OBJ 4
    0x62, // STORE_MAP
    0x10,0x0b, // LOAD_CONST_STRING 'stream'
    0x23,0x05, // LOAD_CONST_OBJ 5
    0x62, // STORE_MAP
    0x10,0x0b, // LOAD_CONST_STRING 'stream'
    0x23,0x06, // LOAD_CONST_OBJ 6
    0x62, // STORE_MAP
    0x16,0x0f, // STORE_NAME '_attrs'
    0x32,0x00, // MAKE_FUNCTION 0
    0x16,0x0c, // STORE_NAME '__getattr__'
    0x51, // LOAD_CONST_NONE
    0x63, // RETURN_VALUE
};
// child of asyncio___init____lt_module_gt_
// frozen bytecode for file asyncio/__init__.py, scope asyncio___init_____getattr__
static const byte fun_data_asyncio___init_____getattr__[48] = {
    0x49,0x04, // prelude
    0x0c,0x10, // names: __getattr__, attr
     // code info
    0x12,0x0f, // LOAD_GLOBAL '_attrs'
    0x14,0x0d, // LOAD_METHOD 'get'
    0xb0, // LOAD_FAST 0
    0x51, // LOAD_CONST_NONE
    0x36,0x02, // CALL_METHOD 2
    0xc1, // STORE_FAST 1
    0xb1, // LOAD_FAST 1
    0x51, // LOAD_CONST_NONE
    0xde, // BINARY_OP 7 <is>
    0x44,0x46, // POP_JUMP_IF_FALSE 6
    0x12,0x11, // LOAD_GLOBAL 'AttributeError'
    0xb0, // LOAD_FAST 0
    0x34,0x01, // CALL_FUNCTION 1
    0x65, // RAISE_OBJ
    0x12,0x12, // LOAD_GLOBAL 'getattr'
    0x12,0x13, // LOAD_GLOBAL '__import__'
    0xb1, // LOAD_FAST 1
    0x51, // LOAD_CONST_NONE
    0x51, // LOAD_CONST_NONE
    0x52, // LOAD_CONST_TRUE
    0x81, // LOAD_CONST_SMALL_INT 1
    0x34,0x05, // CALL_FUNCTION 5
    0xb0, // LOAD_FAST 0
    0x34,0x02, // CALL_FUNCTION 2
    0xc2, // STORE_FAST 2
    0xb2, // LOAD_FAST 2
    0x12,0x14, // LOAD_GLOBAL 'globals'
    0x34,0x00, // CALL_FUNCTION 0
    0xb0, // LOAD_FAST 0
    0x56, // STORE_SUBSCR
    0xb2, // LOAD_FAST 2
    0x63, // RETURN_VALUE
};
#if MICROPY_PERSISTENT_CODE_SAVE
static const mp_raw_code_truncated_t proto_fun_asyncio___init_____getattr__ = {
    .proto_fun_indicator[0] = MP_PROTO_FUN_INDICATOR_RAW_CODE_0,
    .proto_fun_indicator[1] = MP_PROTO_FUN_INDICATOR_RAW_CODE_1,
    .kind = MP_CODE_BYTECODE,
    .is_generator = 0,
    .fun_data = fun_data_asyncio___init_____getattr__,
    .children = NULL,
    #if MICROPY_PERSISTENT_CODE_SAVE
    .fun_data_len = 48,
    .n_children = 0,
    #if MICROPY_EMIT_MACHINE_CODE
    .prelude_offset = 0,
    #endif
    #if MICROPY_PY_SYS_SETTRACE
    .line_of_definition = 0,
    .prelude = {
        .n_state = 10,
        .n_exc_stack = 0,
        .scope_flags = 0,
        .n_pos_args = 1,
        .n_kwonly_args = 0,
        .n_def_pos_args = 0,
        .qstr_block_name_idx = 12,
        .line_info = fun_data_asyncio___init_____getattr__ + 4,
        .line_info_top = fun_data_asyncio___init_____getattr__ + 4,
        .opcodes = fun_data_asyncio___init_____getattr__ + 4,
    },
    #endif
    #endif
};
#else
#define proto_fun_asyncio___init_____getattr__ fun_data_asyncio___init_____getattr__[0]
#endif

static const mp_raw_code_t *const children_asyncio___init____lt_module_gt_[] = {
    (const mp_raw_code_t *)&proto_fun_asyncio___init_____getattr__,
};

static const mp_raw_code_truncated_t proto_fun_asyncio___init____lt_module_gt_ = {
    .proto_fun_indicator[0] = MP_PROTO_FUN_INDICATOR_RAW_CODE_0,
    .proto_fun_indicator[1] = MP_PROTO_FUN_INDICATOR_RAW_CODE_1,
    .kind = MP_CODE_BYTECODE,
    .is_generator = 0,
    .fun_data = fun_data_asyncio___init____lt_module_gt_,
    .children = (void *)&children_asyncio___init____lt_module_gt_,
    #if MICROPY_PERSISTENT_CODE_SAVE
    .fun_data_len = 75,
    .n_children = 1,
    #if MICROPY_EMIT_MACHINE_CODE
    .prelude_offset = 0,
    #endif
    #if MICROPY_PY_SYS_SETTRACE
    .line_of_definition = 0,
    .prelude = {
        .n_state = 3,
        .n_exc_stack = 0,
        .scope_flags = 0,
        .n_pos_args = 0,
        .n_kwonly_args = 0,
        .n_def_pos_args = 0,
        .qstr_block_name_idx = 1,
        .line_info = fun_data_asyncio___init____lt_module_gt_ + 3,
        .line_info_top = fun_data_asyncio___init____lt_module_gt_ + 3,
        .opcodes = fun_data_asyncio___init____lt_module_gt_ + 3,
    },
    #endif
    #endif
};

static const qstr_short_t const_qstr_table_data_asyncio___init__[21] = {
    MP_QSTR_asyncio_slash___init___dot_py,
    MP_QSTR__lt_module_gt_,
    MP_QSTR__star_,
    MP_QSTR_core,
    MP_QSTR_funcs,
    MP_QSTR_wait_for,
    MP_QSTR_gather,
    MP_QSTR_event,
    MP_QSTR_Event,
    MP_QSTR_lock,
    MP_QSTR_Lock,
    MP_QSTR_stream,
    MP_QSTR___getattr__,
    MP_QSTR_get,
    MP_QSTR___version__,
    MP_QSTR__attrs,
    MP_QSTR_attr,
    MP_QSTR_AttributeError,
    MP_QSTR_getattr,
    MP_QSTR___import__,
    MP_QSTR_globals,
};

// constants
static const mp_rom_obj_tuple_t const_obj_asyncio___init___0 = {{&mp_type_tuple}, 3, {
    MP_ROM_INT(3),
    MP_ROM_INT(0),
    MP_ROM_INT(0),
}};

// constant table
static const mp_rom_obj_t const_obj_table_data_asyncio___init__[7] = {
    MP_ROM_PTR(&const_obj_asyncio___init___0),
    MP_ROM_QSTR(MP_QSTR_wait_for_ms),
    MP_ROM_QSTR(MP_QSTR_ThreadSafeFlag),
    MP_ROM_QSTR(MP_QSTR_open_connection),
    MP_ROM_QSTR(MP_QSTR_start_server),
    MP_ROM_QSTR(MP_QSTR_StreamReader),
    MP_ROM_QSTR(MP_QSTR_StreamWriter),
};

static const mp_frozen_module_t frozen_module_asyncio___init__ = {
    .constants = {
        .qstr_table = (qstr_short_t *)&const_qstr_table_data_asyncio___init__,
        .obj_table = (mp_obj_t *)&const_obj_table_data_asyncio___init__,
    },
    .proto_fun = &proto_fun_asyncio___init____lt_module_gt_,
};

////////////////////////////////////////////////////////////////////////////////
// frozen module asyncio_core
// - original source file: /home/atul/micropython/ports/rp2/build-ATRIVATECH_PICUNO/frozen_mpy/asyncio/core.mpy
// - frozen file name: asyncio/core.py
// - .mpy header: 4d:06:00:1f

// frozen bytecode for file asyncio/core.py, scope asyncio_core__lt_module_gt_
static const byte fun_data_asyncio_core__lt_module_gt_[218] = {
    0x2c,0x02, // prelude
    0x01, // names: <module>
     // code info
    0x80, // LOAD_CONST_SMALL_INT 0
    0x10,0x02, // LOAD_CONST_STRING 'ticks_ms'
    0x10,0x03, // LOAD_CONST_STRING 'ticks_diff'
    0x10,0x04, // LOAD_CONST_STRING 'ticks_add'
    0x2a,0x03, // BUILD_TUPLE 3
    0x1b,0x05, // IMPORT_NAME 'time'
    0x1c,0x02, // IMPORT_FROM 'ticks_ms'
    0x16,0x49, // STORE_NAME 'ticks'
    0x1c,0x03, // IMPORT_FROM 'ticks_diff'
    0x16,0x03, // STORE_NAME 'ticks_diff'
    0x1c,0x04, // IMPORT_FROM 'ticks_add'
    0x16,0x04, // STORE_NAME 'ticks_add'
    0x59, // POP_TOP
    0x80, // LOAD_CONST_SMALL_INT 0
    0x51, // LOAD_CONST_NONE
    0x1b,0x06, // IMPORT_NAME 'sys'
    0x16,0x06, // STORE_NAME 'sys'
    0x80, // LOAD_CONST_SMALL_INT 0
    0x51, // LOAD_CONST_NONE
    0x1b,0x07, // IMPORT_NAME 'select'
    0x16,0x07, // STORE_NAME 'select'
    0x48,0x14, // SETUP_EXCEPT 20
    0x80, // LOAD_CONST_SMALL_INT 0
    0x10,0x08, // LOAD_CONST_STRING 'TaskQueue'
    0x10,0x09, // LOAD_CONST_STRING 'Task'
    0x2a,0x02, // BUILD_TUPLE 2
    0x1b,0x0a, // IMPORT_NAME '_asyncio'
    0x1c,0x08, // IMPORT_FROM 'TaskQueue'
    0x16,0x08, // STORE_NAME 'TaskQueue'
    0x1c,0x09, // IMPORT_FROM 'Task'
    0x16,0x09, // STORE_NAME 'Task'
    0x59, // POP_TOP
    0x4a,0x16, // POP_EXCEPT_JUMP 22
    0x59, // POP_TOP
    0x81, // LOAD_CONST_SMALL_INT 1
    0x10,0x08, // LOAD_CONST_STRING 'TaskQueue'
    0x10,0x09, // LOAD_CONST_STRING 'Task'
    0x2a,0x02, // BUILD_TUPLE 2
    0x1b,0x0b, // IMPORT_NAME 'task'
    0x1c,0x08, // IMPORT_FROM 'TaskQueue'
    0x16,0x08, // STORE_NAME 'TaskQueue'
    0x1c,0x09, // IMPORT_FROM 'Task'
    0x16,0x09, // STORE_NAME 'Task'
    0x59, // POP_TOP
    0x4a,0x01, // POP_EXCEPT_JUMP 1
    0x5d, // END_FINALLY
    0x54, // LOAD_BUILD_CLASS
    0x32,0x00, // MAKE_FUNCTION 0
    0x10,0x0c, // LOAD_CONST_STRING 'CancelledError'
    0x11,0x4a, // LOAD_NAME 'BaseException'
    0x34,0x03, // CALL_FUNCTION 3
    0x16,0x0c, // STORE_NAME 'CancelledError'
    0x54, // LOAD_BUILD_CLASS
    0x32,0x01, // MAKE_FUNCTION 1
    0x10,0x0d, // LOAD_CONST_STRING 'TimeoutError'
    0x11,0x4b, // LOAD_NAME 'Exception'
    0x34,0x03, // CALL_FUNCTION 3
    0x16,0x0d, // STORE_NAME 'TimeoutError'
    0x2c,0x03, // BUILD_MAP 3
    0x23,0x00, // LOAD_CONST_OBJ 0
    0x10,0x0e, // LOAD_CONST_STRING 'message'
    0x62, // STORE_MAP
    0x51, // LOAD_CONST_NONE
    0x10,0x0f, // LOAD_CONST_STRING 'exception'
    0x62, // STORE_MAP
    0x51, // LOAD_CONST_NONE
    0x10,0x10, // LOAD_CONST_STRING 'future'
    0x62, // STORE_MAP
    0x16,0x4c, // STORE_NAME '_exc_context'
    0x54, // LOAD_BUILD_CLASS
    0x32,0x02, // MAKE_FUNCTION 2
    0x10,0x11, // LOAD_CONST_STRING 'SingletonGenerator'
    0x34,0x02, // CALL_FUNCTION 2
    0x16,0x11, // STORE_NAME 'SingletonGenerator'
    0x11,0x11, // LOAD_NAME 'SingletonGenerator'
    0x34,0x00, // CALL_FUNCTION 0
    0x2a,0x01, // BUILD_TUPLE 1
    0x53, // LOAD_NULL
    0x33,0x03, // MAKE_FUNCTION_DEFARGS 3
    0x16,0x14, // STORE_NAME 'sleep_ms'
    0x32,0x04, // MAKE_FUNCTION 4
    0x16,0x16, // STORE_NAME 'sleep'
    0x54, // LOAD_BUILD_CLASS
    0x32,0x05, // MAKE_FUNCTION 5
    0x10,0x12, // LOAD_CONST_STRING 'IOQueue'
    0x34,0x02, // CALL_FUNCTION 2
    0x16,0x12, // STORE_NAME 'IOQueue'
    0x32,0x06, // MAKE_FUNCTION 6
    0x16,0x17, // STORE_NAME '_promote_to_task'
    0x32,0x07, // MAKE_FUNCTION 7
    0x16,0x18, // STORE_NAME 'create_task'
    0x51, // LOAD_CONST_NONE
    0x2a,0x01, // BUILD_TUPLE 1
    0x53, // LOAD_NULL
    0x33,0x08, // MAKE_FUNCTION_DEFARGS 8
    0x16,0x1b, // STORE_NAME 'run_until_complete'
    0x32,0x09, // MAKE_FUNCTION 9
    0x16,0x26, // STORE_NAME 'run'
    0x32,0x0a, // MAKE_FUNCTION 10
    0x16,0x27, // STORE_NAME '_stopper'
    0x51, // LOAD_CONST_NONE
    0x17,0x4d, // STORE_GLOBAL 'cur_task'
    0x51, // LOAD_CONST_NONE
    0x17,0x4e, // STORE_GLOBAL '_stop_task'
    0x54, // LOAD_BUILD_CLASS
    0x32,0x0b, // MAKE_FUNCTION 11
    0x10,0x13, // LOAD_CONST_STRING 'Loop'
    0x34,0x02, // CALL_FUNCTION 2
    0x16,0x13, // STORE_NAME 'Loop'
    0x80, // LOAD_CONST_SMALL_INT 0
    0x80, // LOAD_CONST_SMALL_INT 0
    0x2a,0x02, // BUILD_TUPLE 2
    0x53, // LOAD_NULL
    0x33,0x0c, // MAKE_FUNCTION_DEFARGS 12
    0x16,0x28, // STORE_NAME 'get_event_loop'
    0x32,0x0d, // MAKE_FUNCTION 13
    0x16,0x29, // STORE_NAME 'current_task'
    0x32,0x0e, // MAKE_FUNCTION 14
    0x16,0x2a, // STORE_NAME 'new_event_loop'
    0x11,0x2a, // LOAD_NAME 'new_event_loop'
    0x34,0x00, // CALL_FUNCTION 0
    0x59, // POP_TOP
    0x51, // LOAD_CONST_NONE
    0x63, // RETURN_VALUE
};
// child of asyncio_core__lt_module_gt_
// frozen bytecode for file asyncio/core.py, scope asyncio_core_CancelledError
static const byte fun_data_asyncio_core_CancelledError[13] = {
    0x00,0x02, // prelude
    0x0c, // names: CancelledError
     // code info
    0x11,0x4f, // LOAD_NAME '__name__'
    0x16,0x50, // STORE_NAME '__module__'
    0x10,0x0c, // LOAD_CONST_STRING 'CancelledError'
    0x16,0x51, // STORE_NAME '__qualname__'
    0x51, // LOAD_CONST_NONE
    0x63, // RETURN_VALUE
};
#if MICROPY_PERSISTENT_CODE_SAVE
static const mp_raw_code_truncated_t proto_fun_asyncio_core_CancelledError = {
    .proto_fun_indicator[0] = MP_PROTO_FUN_INDICATOR_RAW_CODE_0,
    .proto_fun_indicator[1] = MP_PROTO_FUN_INDICATOR_RAW_CODE_1,
    .kind = MP_CODE_BYTECODE,
    .is_generator = 0,
    .fun_data = fun_data_asyncio_core_CancelledError,
    .children = NULL,
    #if MICROPY_PERSISTENT_CODE_SAVE
    .fun_data_len = 13,
    .n_children = 0,
    #if MICROPY_EMIT_MACHINE_CODE
    .prelude_offset = 0,
    #endif
    #if MICROPY_PY_SYS_SETTRACE
    .line_of_definition = 0,
    .prelude = {
        .n_state = 1,
        .n_exc_stack = 0,
        .scope_flags = 0,
        .n_pos_args = 0,
        .n_kwonly_args = 0,
        .n_def_pos_args = 0,
        .qstr_block_name_idx = 12,
        .line_info = fun_data_asyncio_core_CancelledError + 3,
        .line_info_top = fun_data_asyncio_core_CancelledError + 3,
        .opcodes = fun_data_asyncio_core_CancelledError + 3,
    },
    #endif
    #endif
};
#else
#define proto_fun_asyncio_core_CancelledError fun_data_asyncio_core_CancelledError[0]
#endif

// child of asyncio_core__lt_module_gt_
// frozen bytecode for file asyncio/core.py, scope asyncio_core_TimeoutError
static const byte fun_data_asyncio_core_TimeoutError[13] = {
    0x00,0x02, // prelude
    0x0d, // names: TimeoutError
     // code info
    0x11,0x4f, // LOAD_NAME '__name__'
    0x16,0x50, // STORE_NAME '__module__'
    0x10,0x0d, // LOAD_CONST_STRING 'TimeoutError'
    0x16,0x51, // STORE_NAME '__qualname__'
    0x51, // LOAD_CONST_NONE
    0x63, // RETURN_VALUE
};
#if MICROPY_PERSISTENT_CODE_SAVE
static const mp_raw_code_truncated_t proto_fun_asyncio_core_TimeoutError = {
    .proto_fun_indicator[0] = MP_PROTO_FUN_INDICATOR_RAW_CODE_0,
    .proto_fun_indicator[1] = MP_PROTO_FUN_INDICATOR_RAW_CODE_1,
    .kind = MP_CODE_BYTECODE,
    .is_generator = 0,
    .fun_data = fun_data_asyncio_core_TimeoutError,
    .children = NULL,
    #if MICROPY_PERSISTENT_CODE_SAVE
    .fun_data_len = 13,
    .n_children = 0,
    #if MICROPY_EMIT_MACHINE_CODE
    .prelude_offset = 0,
    #endif
    #if MICROPY_PY_SYS_SETTRACE
    .line_of_definition = 0,
    .prelude = {
        .n_state = 1,
        .n_exc_stack = 0,
        .scope_flags = 0,
        .n_pos_args = 0,
        .n_kwonly_args = 0,
        .n_def_pos_args = 0,
        .qstr_block_name_idx = 13,
        .line_info = fun_data_asyncio_core_TimeoutError + 3,
        .line_info_top = fun_data_asyncio_core_TimeoutError + 3,
        .opcodes = fun_data_asyncio_core_TimeoutError + 3,
    },
    #endif
    #endif
};
#else
#define proto_fun_asyncio_core_TimeoutError fun_data_asyncio_core_TimeoutError[0]
#endif

// child of asyncio_core__lt_module_gt_
// frozen bytecode for file asyncio/core.py, scope asyncio_core_SingletonGenerator
static const byte fun_data_asyncio_core_SingletonGenerator[25] = {
    0x00,0x02, // prelude
    0x11, // names: SingletonGenerator
     // code info
    0x11,0x4f, // LOAD_NAME '__name__'
    0x16,0x50, // STORE_NAME '__module__'
    0x10,0x11, // LOAD_CONST_STRING 'SingletonGenerator'
    0x16,0x51, // STORE_NAME '__qualname__'
    0x32,0x00, // MAKE_FUNCTION 0
    0x16,0x2b, // STORE_NAME '__init__'
    0x32,0x01, // MAKE_FUNCTION 1
    0x16,0x2d, // STORE_NAME '__iter__'
    0x32,0x02, // MAKE_FUNCTION 2
    0x16,0x2e, // STORE_NAME '__next__'
    0x51, // LOAD_CONST_NONE
    0x63, // RETURN_VALUE
};
// child of asyncio_core_SingletonGenerator
// frozen bytecode for file asyncio/core.py, scope asyncio_core_SingletonGenerator___init__
static const byte fun_data_asyncio_core_SingletonGenerator___init__[17] = {
    0x11,0x04, // prelude
    0x2b,0x63, // names: __init__, self
     // code info
    0x51, // LOAD_CONST_NONE
    0xb0, // LOAD_FAST 0
    0x18,0x15, // STORE_ATTR 'state'
    0x12,0x5d, // LOAD_GLOBAL 'StopIteration'
    0x34,0x00, // CALL_FUNCTION 0
    0xb0, // LOAD_FAST 0
    0x18,0x2c, // STORE_ATTR 'exc'
    0x51, // LOAD_CONST_NONE
    0x63, // RETURN_VALUE
};
#if MICROPY_PERSISTENT_CODE_SAVE
static const mp_raw_code_truncated_t proto_fun_asyncio_core_SingletonGenerator___init__ = {
    .proto_fun_indicator[0] = MP_PROTO_FUN_INDICATOR_RAW_CODE_0,
    .proto_fun_indicator[1] = MP_PROTO_FUN_INDICATOR_RAW_CODE_1,
    .kind = MP_CODE_BYTECODE,
    .is_generator = 0,
    .fun_data = fun_data_asyncio_core_SingletonGenerator___init__,
    .children = NULL,
    #if MICROPY_PERSISTENT_CODE_SAVE
    .fun_data_len = 17,
    .n_children = 0,
    #if MICROPY_EMIT_MACHINE_CODE
    .prelude_offset = 0,
    #endif
    #if MICROPY_PY_SYS_SETTRACE
    .line_of_definition = 0,
    .prelude = {
        .n_state = 3,
        .n_exc_stack = 0,
        .scope_flags = 0,
        .n_pos_args = 1,
        .n_kwonly_args = 0,
        .n_def_pos_args = 0,
        .qstr_block_name_idx = 43,
        .line_info = fun_data_asyncio_core_SingletonGenerator___init__ + 4,
        .line_info_top = fun_data_asyncio_core_SingletonGenerator___init__ + 4,
        .opcodes = fun_data_asyncio_core_SingletonGenerator___init__ + 4,
    },
    #endif
    #endif
};
#else
#define proto_fun_asyncio_core_SingletonGenerator___init__ fun_data_asyncio_core_SingletonGenerator___init__[0]
#endif

// child of asyncio_core_SingletonGenerator
// frozen bytecode for file asyncio/core.py, scope asyncio_core_SingletonGenerator___iter__
static const byte fun_data_asyncio_core_SingletonGenerator___iter__[6] = {
    0x09,0x04, // prelude
    0x2d,0x63, // names: __iter__, self
     // code info
    0xb0, // LOAD_FAST 0
    0x63, // RETURN_VALUE
};
#if MICROPY_PERSISTENT_CODE_SAVE
static const mp_raw_code_truncated_t proto_fun_asyncio_core_SingletonGenerator___iter__ = {
    .proto_fun_indicator[0] = MP_PROTO_FUN_INDICATOR_RAW_CODE_0,
    .proto_fun_indicator[1] = MP_PROTO_FUN_INDICATOR_RAW_CODE_1,
    .kind = MP_CODE_BYTECODE,
    .is_generator = 0,
    .fun_data = fun_data_asyncio_core_SingletonGenerator___iter__,
    .children = NULL,
    #if MICROPY_PERSISTENT_CODE_SAVE
    .fun_data_len = 6,
    .n_children = 0,
    #if MICROPY_EMIT_MACHINE_CODE
    .prelude_offset = 0,
    #endif
    #if MICROPY_PY_SYS_SETTRACE
    .line_of_definition = 0,
    .prelude = {
        .n_state = 2,
        .n_exc_stack = 0,
        .scope_flags = 0,
        .n_pos_args = 1,
        .n_kwonly_args = 0,
        .n_def_pos_args = 0,
        .qstr_block_name_idx = 45,
        .line_info = fun_data_asyncio_core_SingletonGenerator___iter__ + 4,
        .line_info_top = fun_data_asyncio_core_SingletonGenerator___iter__ + 4,
        .opcodes = fun_data_asyncio_core_SingletonGenerator___iter__ + 4,
    },
    #endif
    #endif
};
#else
#define proto_fun_asyncio_core_SingletonGenerator___iter__ fun_data_asyncio_core_SingletonGenerator___iter__[0]
#endif

// child of asyncio_core_SingletonGenerator
// frozen bytecode for file asyncio/core.py, scope asyncio_core_SingletonGenerator___next__
static const byte fun_data_asyncio_core_SingletonGenerator___next__[42] = {
    0x21,0x04, // prelude
    0x2e,0x63, // names: __next__, self
     // code info
    0xb0, // LOAD_FAST 0
    0x13,0x15, // LOAD_ATTR 'state'
    0x51, // LOAD_CONST_NONE
    0xde, // BINARY_OP 7 <is>
    0xd3, // UNARY_OP 3 <not>
    0x44,0x52, // POP_JUMP_IF_FALSE 18
    0x12,0x5b, // LOAD_GLOBAL '_task_queue'
    0x14,0x1a, // LOAD_METHOD 'push'
    0x12,0x4d, // LOAD_GLOBAL 'cur_task'
    0xb0, // LOAD_FAST 0
    0x13,0x15, // LOAD_ATTR 'state'
    0x36,0x02, // CALL_METHOD 2
    0x59, // POP_TOP
    0x51, // LOAD_CONST_NONE
    0xb0, // LOAD_FAST 0
    0x18,0x15, // STORE_ATTR 'state'
    0x51, // LOAD_CONST_NONE
    0x63, // RETURN_VALUE
    0x51, // LOAD_CONST_NONE
    0xb0, // LOAD_FAST 0
    0x13,0x2c, // LOAD_ATTR 'exc'
    0x18,0x2f, // STORE_ATTR '__traceback__'
    0xb0, // LOAD_FAST 0
    0x13,0x2c, // LOAD_ATTR 'exc'
    0x65, // RAISE_OBJ
    0x51, // LOAD_CONST_NONE
    0x63, // RETURN_VALUE
};
#if MICROPY_PERSISTENT_CODE_SAVE
static const mp_raw_code_truncated_t proto_fun_asyncio_core_SingletonGenerator___next__ = {
    .proto_fun_indicator[0] = MP_PROTO_FUN_INDICATOR_RAW_CODE_0,
    .proto_fun_indicator[1] = MP_PROTO_FUN_INDICATOR_RAW_CODE_1,
    .kind = MP_CODE_BYTECODE,
    .is_generator = 0,
    .fun_data = fun_data_asyncio_core_SingletonGenerator___next__,
    .children = NULL,
    #if MICROPY_PERSISTENT_CODE_SAVE
    .fun_data_len = 42,
    .n_children = 0,
    #if MICROPY_EMIT_MACHINE_CODE
    .prelude_offset = 0,
    #endif
    #if MICROPY_PY_SYS_SETTRACE
    .line_of_definition = 0,
    .prelude = {
        .n_state = 5,
        .n_exc_stack = 0,
        .scope_flags = 0,
        .n_pos_args = 1,
        .n_kwonly_args = 0,
        .n_def_pos_args = 0,
        .qstr_block_name_idx = 46,
        .line_info = fun_data_asyncio_core_SingletonGenerator___next__ + 4,
        .line_info_top = fun_data_asyncio_core_SingletonGenerator___next__ + 4,
        .opcodes = fun_data_asyncio_core_SingletonGenerator___next__ + 4,
    },
    #endif
    #endif
};
#else
#define proto_fun_asyncio_core_SingletonGenerator___next__ fun_data_asyncio_core_SingletonGenerator___next__[0]
#endif

static const mp_raw_code_t *const children_asyncio_core_SingletonGenerator[] = {
    (const mp_raw_code_t *)&proto_fun_asyncio_core_SingletonGenerator___init__,
    (const mp_raw_code_t *)&proto_fun_asyncio_core_SingletonGenerator___iter__,
    (const mp_raw_code_t *)&proto_fun_asyncio_core_SingletonGenerator___next__,
};
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
